chindynamics/Delta-Assistance/src/HCI/favoriteicons_rc.py

# Resource object code (Python 3)
# Created by: object code
# Created by: The Resource Compiler for Qt version 5.15.2
# WARNING! All changes made in this file will be lost!

from PySide6 import QtCore

qt_resource_data = b"\
\x00\x00\x01\xae\
<\
svg xmlns=\x22http:\
//www.w3.org/200\
0/svg\x22 width=\x2232\
\x22 height=\x2232\x22 vi\
ewBox=\x220 0 24 24\
\x22><path fill=\x22#f\
fffff\x22 d=\x22M11.07\
 12.85c.77-1.39 \
2.25-2.21 3.11-3\
.44c.91-1.29.4-3\
.7-2.18-3.7c-1.6\
9 0-2.52 1.28-2.\
87 2.34L6.54 6.9\
6C7.25 4.83 9.18\
 3 11.99 3c2.35 \
0 3.96 1.07 4.78\
 2.41c.7 1.15 1.\
11 3.3.03 4.9c-1\
.2 1.77-2.35 2.3\
1-2.97 3.45c-.25\
.46-.35.76-.35 2\
.24h-2.89c-.01-.\
78-.13-2.05.48-3\
.15M14 20c0 1.1-\
.9 2-2 2s-2-.9-2\
-2s.9-2 2-2s2 .9\
 2 2\x22/></svg>\
\x00\x00\x00\xf1\
<\
svg xmlns=\x22http:\
//www.w3.org/200\
0/svg\x22 width=\x2232\
\x22 height=\x2232\x22 vi\
ewBox=\x220 0 24 24\
\x22><path fill=\x22no\
ne\x22 stroke=\x22#fff\
fff\x22 stroke-line\
cap=\x22round\x22 stro\
ke-linejoin=\x22rou\
nd\x22 stroke-width\
=\x221.5\x22 d=\x22m17 17\
l4 4M3 11a8 8 0 \
1 0 16 0a8 8 0 0\
 0-16 0\x22/></svg>\
\
\x00\x00\x01t\
<\
svg xmlns=\x22http:\
//www.w3.org/200\
0/svg\x22 width=\x2232\
\x22 height=\x2232\x22 vi\
ewBox=\x220 0 24 24\
\x22><!-- Icon from\
 Huge Icons by H\
ugeicons - undef\
ined --><g fill=\
\x22none\x22 stroke=\x22#\
ffffff\x22 stroke-l\
inecap=\x22round\x22 s\
troke-linejoin=\x22\
round\x22 stroke-wi\
dth=\x221.5\x22 color=\
\x22#ffffff\x22><circl\
e cx=\x2212\x22 cy=\x2212\
\x22 r=\x2210\x22/><path \
d=\x22M8 12h8m-8 0c\
0-.7 1.994-2.008\
 2.5-2.5M8 12c0 \
.7 1.994 2.008 2\
.5 2.5\x22/></g></s\
vg>\
\x00\x00\x02,\
<\
svg xmlns=\x22http:\
//www.w3.org/200\
0/svg\x22 width=\x2232\
\x22 height=\x2232\x22 vi\
ewBox=\x220 0 24 24\
\x22><!-- Icon from\
 Google Material\
 Icons by Materi\
al Design Author\
s - https://gith\
ub.com/material-\
icons/material-i\
cons/blob/master\
/LICENSE --><pat\
h fill=\x22#ffffff\x22\
 d=\x22M22 12c0 5.5\
2-4.48 10-10 10S\
2 17.52 2 12c0-1\
.19.22-2.32.6-3.\
38l1.88.68C4.17 \
10.14 4 11.05 4 \
12c0 4.41 3.59 8\
 8 8s8-3.59 8-8s\
-3.59-8-8-8c-.95\
 0-1.85.17-2.69.\
48l-.68-1.89C9.6\
9 2.22 10.82 2 1\
2 2c5.52 0 10 4.\
48 10 10M5.5 4C4\
.67 4 4 4.67 4 5\
.5S4.67 7 5.5 7S\
7 6.33 7 5.5S6.3\
3 4 5.5 4M11 16V\
8H9v8zm4 0V8h-2v\
8z\x22/></svg>\
\x00\x00\x025\
<\
svg xmlns=\x22http:\
//www.w3.org/200\
0/svg\x22 width=\x2232\
\x22 height=\x2232\x22 vi\
ewBox=\x220 0 48 48\
\x22><!-- Icon from\
 Health Icons by\
 Resolve to Save\
 Lives - https:/\
/github.com/reso\
lvetosavelives/h\
ealthicons/blob/\
main/LICENSE -->\
<path fill=\x22#fff\
fff\x22 d=\x22M9 19.03\
5C9 13.309 12.81\
2 8 18.031 8c3.6\
22 0 6.31 2.382 \
7.969 5.761C27.6\
59 10.382 30.347\
 8 33.969 8C39.1\
89 8 43 13.31 43\
 19.035C43 31.28\
9 26 40 26 40s-1\
1.451-5.513-15.5\
57-14.556h10.142\
l1.612-2.865l1.8\
83 6.59l4.41-5.6\
69H34v-2h-6.49l-\
2.59 3.33l-2.117\
-7.409l-3.388 6.\
023H9.68q.32 1.0\
28.763 2H6v-2h3.\
68a14.8 14.8 0 0\
 1-.68-4.41\x22/></\
svg>\
\x00\x00\x02\xe0\
<\
svg xmlns=\x22http:\
//www.w3.org/200\
0/svg\x22 width=\x2232\
\x22 height=\x2232\x22 vi\
ewBox=\x220 0 24 24\
\x22><!-- Icon from\
 Huge Icons by H\
ugeicons - undef\
ined --><path fi\
ll=\x22none\x22 stroke\
=\x22#ffffff\x22 strok\
e-linecap=\x22round\
\x22 stroke-linejoi\
n=\x22round\x22 stroke\
-width=\x221.5\x22 d=\x22\
M2.008 15.81c.22\
3-3.494.88-6.05 \
1.435-7.535c.281\
-.75.885-1.308 1\
.658-1.495c4.3-1\
.04 9.498-1.04 1\
3.798 0c.773.187\
 1.377.745 1.658\
 1.495c.556 1.48\
5 1.212 4.041 1.\
435 7.534c.133 2\
.09-1.377 3.241-\
3.05 4.083c-1.06\
4.537-1.883-1.04\
6-2.427-2.272a1.\
82 1.82 0 0 0-1.\
687-1.084H9.172c\
-.739 0-1.39.415\
-1.687 1.084c-.5\
44 1.226-1.363 2\
.809-2.428 2.272\
c-1.655-.833-3.1\
83-1.976-3.049-4\
.083M5 4.5L6.963\
 4M19 4.5L17 4m-\
8 9l-1.5-1.5m0 0\
L6 10m1.5 1.5L6 \
13m1.5-1.5L9 10m\
6.988 0h.01m1.99\
 3h.01\x22 color=\x22#\
ffffff\x22/></svg>\
\x00\x00\x1b\x90\
<\
?xml version=\x221.\
0\x22 encoding=\x22utf\
-8\x22?>\x0a<!-- Gener\
ator: Adobe Adob\
e Illustrator 24\
.2.0, SVG Export\
 Plug-In . SVG V\
ersion: 6.00 Bui\
ld 0)  -->\x0a<svg \
version=\x221.1\x22 xm\
lns=\x22http://www.\
w3.org/2000/svg\x22\
 xmlns:xlink=\x22ht\
tp://www.w3.org/\
1999/xlink\x22 x=\x220\
px\x22 y=\x220px\x22\x0a\x09 wi\
dth=\x22595.28px\x22 h\
eight=\x22560.42px\x22\
 viewBox=\x220 0 59\
5.28 560.42\x22 sty\
le=\x22enable-backg\
round:new 0 0 59\
5.28 560.42;\x22\x0a\x09 \
xml:space=\x22prese\
rve\x22>\x0a<style typ\
e=\x22text/css\x22>\x0a\x09.\
st0{fill:#F4BAA6\
;stroke:#F4BAA6;\
stroke-width:5;s\
troke-miterlimit\
:10;}\x0a\x09.st1{disp\
lay:none;}\x0a\x09.st2\
{fill:#F4BAA6;st\
roke:#DB9E8A;str\
oke-width:5;stro\
ke-miterlimit:10\
;}\x0a\x09.st3{display\
:none;fill:#29AB\
E2;stroke:#00000\
0;stroke-width:5\
;stroke-miterlim\
it:10;}\x0a\x09.st4{fi\
ll:#E6E6E6;strok\
e:#E6E6E6;stroke\
-width:5;stroke-\
miterlimit:10;}\x0a\
\x09.st5{fill:#92CE\
E8;stroke:#92CEE\
8;stroke-width:5\
;stroke-miterlim\
it:10;}\x0a\x09.st6{fi\
ll:#29ABE2;strok\
e:#29ABE2;stroke\
-width:5;stroke-\
miterlimit:10;}\x0a\
\x09.st7{fill:#B3B3\
B3;stroke:#B3B3B\
3;stroke-width:5\
;stroke-miterlim\
it:10;}\x0a\x09.st8{fi\
ll:#E6E6E6;strok\
e:#D9D9D9;stroke\
-width:5;stroke-\
miterlimit:10;}\x0a\
\x09.st9{fill:#E6E6\
E6;stroke:#B3B3B\
3;stroke-width:5\
;stroke-miterlim\
it:10;}\x0a\x09.st10{f\
ill:#C48F7E;}\x0a\x09.\
st11{fill:#E6B5A\
5;}\x0a\x09.st12{fill:\
#F4BAA6;}\x0a\x09.st13\
{fill:#EDC1B2;}\x0a\
\x09.st14{fill:#F4B\
AA6;stroke:#F4BA\
A6;stroke-miterl\
imit:10;}\x0a\x09.st15\
{fill:#FF6B89;st\
roke:#FF6B89;str\
oke-miterlimit:1\
0;}\x0a\x09.st16{fill:\
none;stroke:#8A8\
A8A;stroke-width\
:5;stroke-miterl\
imit:10;}\x0a\x09.st17\
{fill:#92CEE8;}\x0a\
\x09.st18{fill:#F5F\
5F5;}\x0a\x09.st19{fil\
l:none;stroke:#9\
2CEE8;stroke-wid\
th:5;stroke-mite\
rlimit:10;}\x0a\x09.st\
20{fill:#855B4E;\
}\x0a\x09.st21{fill:#A\
37364;}\x0a\x09.st22{f\
ill:#EBCE42;}\x0a\x09.\
st23{fill:#94949\
4;stroke:#949494\
;stroke-width:5;\
stroke-miterlimi\
t:10;}\x0a\x09.st24{st\
roke:#000000;str\
oke-miterlimit:1\
0;}\x0a\x09.st25{fill:\
#F5F5F5;stroke:#\
F5F5F5;stroke-wi\
dth:5;stroke-mit\
erlimit:10;}\x0a\x09.s\
t26{fill:#FFFFFF\
;}\x0a\x09.st27{fill:#\
A37364;stroke:#A\
37364;stroke-wid\
th:5;stroke-mite\
rlimit:10;}\x0a\x09.st\
28{fill:#A37364;\
stroke:#A37364;s\
troke-width:3;st\
roke-miterlimit:\
10;}\x0a\x09.st29{fill\
:#6B9DB3;stroke:\
#6B9DB3;stroke-w\
idth:5;stroke-mi\
terlimit:10;}\x0a\x09.\
st30{fill:#DB9E8\
A;stroke:#346C85\
;stroke-width:5;\
stroke-miterlimi\
t:10;}\x0a\x09.st31{fi\
ll:#346C85;strok\
e:#346C85;stroke\
-width:5;stroke-\
miterlimit:10;}\x0a\
\x09.st32{fill:#2A6\
27A;stroke:#2A62\
7A;stroke-width:\
5;stroke-miterli\
mit:10;}\x0a\x09.st33{\
fill:#6B9DB3;}\x0a\x09\
.st34{fill:#EDED\
ED;}\x0a\x09.st35{fill\
:none;stroke:#32\
3E9C;stroke-widt\
h:7;stroke-miter\
limit:10;}\x0a\x09.st3\
6{fill:#C23A4E;}\
\x0a\x09.st37{fill:#C2\
3A4E;stroke:#C23\
A4E;stroke-miter\
limit:10;}\x0a\x09.st3\
8{fill:#C23A4E;s\
troke:#C23A4E;st\
roke-width:5;str\
oke-miterlimit:1\
0;}\x0a\x09.st39{fill:\
#8A8A8A;stroke:#\
323E9C;stroke-wi\
dth:7;stroke-mit\
erlimit:10;}\x0a\x09.s\
t40{fill:#323E9C\
;stroke:#323E9C;\
stroke-miterlimi\
t:10;}\x0a\x09.st41{fi\
ll:#79C77F;}\x0a\x09.s\
t42{opacity:0.72\
94;fill:#8DB9CC;\
}\x0a\x09.st43{fill:#D\
B9E8A;stroke:#DB\
9E8A;stroke-mite\
rlimit:10;}\x0a\x09.st\
44{opacity:0.588\
2;fill:#FFFF00;}\
\x0a\x09.st45{fill:#8C\
C63F;stroke:#8CC\
63F;stroke-miter\
limit:10;}\x0a\x09.st4\
6{fill:#FF0000;}\
\x0a\x09.st47{fill:#C1\
272D;}\x0a\x09.st48{fi\
ll:#8CC63F;strok\
e:#80B53A;stroke\
-miterlimit:10;}\
\x0a\x09.st49{opacity:\
0.9608;fill:#FF0\
000;}\x0a\x09.st50{opa\
city:0.949;fill:\
#C1272D;}\x0a\x09.st51\
{fill:#FFFD7A;st\
roke:#FFFD7A;str\
oke-miterlimit:1\
0;}\x0a\x09.st52{fill:\
#8CC63F;}\x0a\x09.st53\
{fill:#B38576;st\
roke:#B38576;str\
oke-miterlimit:1\
0;}\x0a\x09.st54{opaci\
ty:0.7412;fill:#\
9E68A3;stroke:#9\
E68A3;stroke-mit\
erlimit:10;}\x0a\x09.s\
t55{opacity:0.50\
2;stroke:#000000\
;stroke-miterlim\
it:10;}\x0a\x09.st56{f\
ill:#C48F7E;stro\
ke:#C48F7E;strok\
e-miterlimit:10;\
}\x0a\x09.st57{fill:#8\
55B4E;stroke:#85\
5B4E;stroke-mite\
rlimit:10;}\x0a\x09.st\
58{opacity:0.670\
6;fill:#F15A24;}\
\x0a\x09.st59{fill:#9E\
005D;}\x0a\x09.st60{op\
acity:0.6784;fil\
l:#FFFFFF;stroke\
:#FFFFFF;stroke-\
miterlimit:10;}\x0a\
\x09.st61{opacity:0\
.6588;fill:#FFFD\
7A;stroke:#FFFD7\
A;stroke-miterli\
mit:10;}\x0a\x09.st62{\
fill:#949494;str\
oke:#949494;stro\
ke-miterlimit:10\
;}\x0a\x09.st63{fill:n\
one;stroke:#9494\
94;stroke-width:\
3;stroke-miterli\
mit:10;}\x0a\x09.st64{\
fill:#FFFD7A;str\
oke:#EDEB77;stro\
ke-miterlimit:10\
;}\x0a\x09.st65{fill:#\
FF9191;stroke:#F\
F9191;stroke-mit\
erlimit:10;}\x0a\x09.s\
t66{fill:#FFFFFF\
;stroke:#FFFFFF;\
stroke-miterlimi\
t:10;}\x0a</style>\x0a\
<g id=\x22Layer_1\x22>\
\x0a</g>\x0a<g id=\x22Lay\
er_2\x22>\x0a</g>\x0a<g i\
d=\x22Layer_3\x22>\x0a\x09<p\
ath class=\x22st11\x22\
 d=\x22M180.65,344.\
7l0.71-35.33c0.0\
5-2.59,1.79-4.83\
,4.29-5.53l9.46-\
2.64c18.97-5.29,\
36.82,11.33,32.9\
1,30.63l0,0\x0a\x09\x09l3\
6.18,44.04c2.99,\
3.64,0.56,9.13-4\
.15,9.37l-37.96,\
1.88c-8.69,0.43-\
17.12-3.05-22.97\
-9.49l-10.42-11.\
47\x0a\x09\x09C183.37,360\
.3,180.49,352.62\
,180.65,344.7z\x22/\
>\x0a\x09<path class=\x22\
st12\x22 d=\x22M247.04\
,394.39l-0.54-3.\
41l-40.21-45.27c\
-7.24-8.15-7.34-\
20.89-0.22-29.17\
l0,0\x0a\x09\x09c13.74-15\
.99,36.93-17.32,\
52.2-2.99l32.7,3\
0.7c4.34,4.08,9.\
77,6.61,15.53,7.\
23l27.08,2.93c6.\
66,0.72,12.96,3.\
55,18.1,8.12\x0a\x09\x09l\
6.94,6.16c6.2,5.\
5,3.93,16.19-3.8\
8,18.31l-85.03,2\
3.12C259.3,412.9\
6,248.84,405.7,2\
47.04,394.39z\x22/>\
\x0a\x09<path class=\x22s\
t13\x22 d=\x22M215.82,\
380.45l-34.68-35\
.97c-1.58-1.64-2\
.63-3.71-3.03-5.\
94l-0.22-1.23c-4\
.15-23.47-27.48-\
38.39-50.53-32.3\
1\x0a\x09\x09l-5.63,1.48l\
9.1,44.63l34.3,3\
2.64L215.82,380.\
45z\x22/>\x0a\x09<path cl\
ass=\x22st14\x22 d=\x22M5\
15.8,452.48l-335\
.96-1.12c-9.87-0\
.03-19.33-3.97-2\
6.31-10.95l-65.5\
3-65.49\x0a\x09\x09c-5.45\
-5.44-8.51-12.83\
-8.51-20.53v-36.\
17c0-10.6,8.5-19\
.23,19.1-19.39h0\
c18.13-0.28,33.8\
1,12.57,37.1,30.\
4l2.06,11.2\x0a\x09\x09c0\
.37,2.02,1.35,3.\
88,2.8,5.33l30.8\
4,30.82c2.52,2.5\
2,5.96,3.91,9.52\
,3.85l63.29-2.06\
l271.59-16.02V45\
2.48z\x22/>\x0a\x09<path \
class=\x22st15\x22 d=\x22\
M275.05,55.15l-1\
0.86-2.92c-23.91\
-9.32-71.75,11.0\
8-86.84,31.76l-1\
3.36,19.61\x0a\x09\x09c-2\
0.8,28.51-10.53,\
69.43,12.09,96.5\
3L296.16,323.8c9\
.4,11.26,26.88,1\
0.86,35.75-0.81l\
123.64-136.55\x0a\x09\x09\
c23.73-31.23,6.4\
1-88.83-19.84-11\
8l0,0c-14.85-16.\
5-53.52-29.92-74\
.12-21.55l-13.68\
,6.98c-2.88,0.9-\
5.64,2.14-8.23,3\
.7\x0a\x09\x09l-27.23,16.\
42c-2.17,0.88-9.\
43-4.3-16.47-9.1\
6C289.61,60.43,2\
82.53,57.16,275.\
05,55.15z\x22/>\x0a\x09<p\
ath class=\x22st16\x22\
 d=\x22M178.85,203.\
03l43.23-0.58l1.\
26-0.45l15.62-57\
.5c0.06-0.21,0.3\
5-0.21,0.41-0.01\
l34.29,110.6\x0a\x09\x09c\
0.12,0.4,0.7,0.3\
5,0.76-0.06l21.6\
9-142.46c0.05-0.\
3,0.47-0.32,0.54\
-0.02l21.13,85.6\
3c0.28,1.15,1.26\
,2,2.44,2.12l22.\
31-0.01\x22/>\x0a\x09<pol\
ygon class=\x22st17\
\x22 points=\x22342.17\
,185.73 359.19,1\
82.05 376.3,179 \
387.04,177.12 40\
1.83,175.96 415.\
03,176.97 426.78\
,178.13 \x0a\x09\x09438.8\
2,179.58 448.1,1\
81.9 459.85,184.\
08 470.3,187.27 \
474.94,191.77 47\
3.2,214.83 473.0\
5,232.24 468.99,\
253.85 463.19,26\
9.66 \x0a\x09\x09455.94,2\
82.28 448.83,291\
.56 440.41,299.9\
7 432.87,307.52 \
423.01,314.91 41\
2.57,322.6 402.8\
5,324.2 395.16,3\
18.54 387.62,308\
.97 \x0a\x09\x09380.07,30\
6.79 367.75,295.\
04 358.61,284.6 \
350.19,275.32 34\
6.13,260.96 342.\
36,247.76 341.06\
,232.53 340.62,2\
14.25 340.77,199\
.46 \x09\x0a\x09\x09\x22/>\x0a\x09<pa\
th class=\x22st18\x22 \
d=\x22M393.78,178.4\
1h27.94c0.29,0,0\
.52,0.24,0.52,0.\
52v140.95c0,0.29\
-0.24,0.52-0.52,\
0.52l-15.75,7.28\
l-12.2-7.28\x0a\x09\x09c-\
0.29,0-0.52-0.24\
-0.52-0.52V178.9\
4C393.26,178.65,\
393.49,178.41,39\
3.78,178.41z\x22/>\x0a\
\x09<rect x=\x22343.96\
\x22 y=\x22221.07\x22 cla\
ss=\x22st18\x22 width=\
\x22129.5\x22 height=\x22\
28.99\x22/>\x0a\x09<path \
class=\x22st19\x22 d=\x22\
M340.75,189.22l2\
.24,55.4c0.81,20\
.12,10.04,38.91,\
25.34,51.65l29.6\
9,24.7c5.25,4.36\
,12.76,4.46,18.1\
,0.22\x0a\x09\x09l20.02-1\
5.87c23.11-18.32\
,36.93-46.25,37.\
63-76.08l0.88-37\
.23c0.89-1.78-0.\
01-3.95-1.88-4.5\
6l-5.66-1.84\x0a\x09\x09c\
-37.14-12.06-76.\
89-13.01-114.54-\
2.73l-10.24,2.8C\
340.84,186.09,34\
0.07,187.79,340.\
75,189.22z\x22/>\x0a\x09<\
line class=\x22st16\
\x22 x1=\x22359.68\x22 y1\
=\x22155.02\x22 x2=\x2235\
9.4\x22 y2=\x22116.26\x22\
/>\x0a\x09<line class=\
\x22st16\x22 x1=\x22342.1\
7\x22 y1=\x22135.64\x22 x\
2=\x22376.33\x22 y2=\x221\
35.64\x22/>\x0a</g>\x0a<g\
 id=\x22Layer_5\x22>\x0a\x09\
<g id=\x22Layer_4\x22>\
\x0a\x09</g>\x0a</g>\x0a<g i\
d=\x22Layer_6\x22>\x0a</g\
>\x0a<g id=\x22Layer_7\
\x22>\x0a</g>\x0a</svg>\x0a\
\x00\x00)\x09\
<\
?xml version=\x221.\
0\x22 encoding=\x22utf\
-8\x22?>\x0a<!-- Gener\
ator: Adobe Adob\
e Illustrator 24\
.2.0, SVG Export\
 Plug-In . SVG V\
ersion: 6.00 Bui\
ld 0)  -->\x0a<svg \
version=\x221.1\x22 xm\
lns=\x22http://www.\
w3.org/2000/svg\x22\
 xmlns:xlink=\x22ht\
tp://www.w3.org/\
1999/xlink\x22 x=\x220\
px\x22 y=\x220px\x22\x0a\x09 wi\
dth=\x22595.28px\x22 h\
eight=\x22555.8px\x22 \
viewBox=\x220 0 595\
.28 555.8\x22 style\
=\x22enable-backgro\
und:new 0 0 595.\
28 555.8;\x22\x0a\x09 xml\
:space=\x22preserve\
\x22>\x0a<style type=\x22\
text/css\x22>\x0a\x09.st0\
{fill:#F4BAA6;st\
roke:#F4BAA6;str\
oke-width:5;stro\
ke-miterlimit:10\
;}\x0a\x09.st1{display\
:none;}\x0a\x09.st2{fi\
ll:#F4BAA6;strok\
e:#DB9E8A;stroke\
-width:5;stroke-\
miterlimit:10;}\x0a\
\x09.st3{display:no\
ne;fill:#29ABE2;\
stroke:#000000;s\
troke-width:5;st\
roke-miterlimit:\
10;}\x0a\x09.st4{fill:\
#E6E6E6;stroke:#\
E6E6E6;stroke-wi\
dth:5;stroke-mit\
erlimit:10;}\x0a\x09.s\
t5{fill:#92CEE8;\
stroke:#92CEE8;s\
troke-width:5;st\
roke-miterlimit:\
10;}\x0a\x09.st6{fill:\
#29ABE2;stroke:#\
29ABE2;stroke-wi\
dth:5;stroke-mit\
erlimit:10;}\x0a\x09.s\
t7{fill:#B3B3B3;\
stroke:#B3B3B3;s\
troke-width:5;st\
roke-miterlimit:\
10;}\x0a\x09.st8{fill:\
#E6E6E6;stroke:#\
D9D9D9;stroke-wi\
dth:5;stroke-mit\
erlimit:10;}\x0a\x09.s\
t9{fill:#E6E6E6;\
stroke:#B3B3B3;s\
troke-width:5;st\
roke-miterlimit:\
10;}\x0a\x09.st10{fill\
:#C48F7E;}\x0a\x09.st1\
1{fill:#E6B5A5;}\
\x0a\x09.st12{fill:#F4\
BAA6;}\x0a\x09.st13{fi\
ll:#EDC1B2;}\x0a\x09.s\
t14{fill:#F4BAA6\
;stroke:#F4BAA6;\
stroke-miterlimi\
t:10;}\x0a\x09.st15{fi\
ll:#FF6B89;strok\
e:#FF6B89;stroke\
-miterlimit:10;}\
\x0a\x09.st16{fill:non\
e;stroke:#8A8A8A\
;stroke-width:5;\
stroke-miterlimi\
t:10;}\x0a\x09.st17{fi\
ll:#92CEE8;}\x0a\x09.s\
t18{fill:#F5F5F5\
;}\x0a\x09.st19{fill:n\
one;stroke:#92CE\
E8;stroke-width:\
5;stroke-miterli\
mit:10;}\x0a\x09.st20{\
fill:#855B4E;}\x0a\x09\
.st21{fill:#A373\
64;}\x0a\x09.st22{fill\
:#EBCE42;}\x0a\x09.st2\
3{fill:#949494;s\
troke:#949494;st\
roke-width:5;str\
oke-miterlimit:1\
0;}\x0a\x09.st24{strok\
e:#000000;stroke\
-miterlimit:10;}\
\x0a\x09.st25{fill:#F5\
F5F5;stroke:#F5F\
5F5;stroke-width\
:5;stroke-miterl\
imit:10;}\x0a\x09.st26\
{fill:#FFFFFF;}\x0a\
\x09.st27{fill:#A37\
364;stroke:#A373\
64;stroke-width:\
5;stroke-miterli\
mit:10;}\x0a\x09.st28{\
fill:#A37364;str\
oke:#A37364;stro\
ke-width:3;strok\
e-miterlimit:10;\
}\x0a\x09.st29{fill:#6\
B9DB3;stroke:#6B\
9DB3;stroke-widt\
h:5;stroke-miter\
limit:10;}\x0a\x09.st3\
0{fill:#DB9E8A;s\
troke:#346C85;st\
roke-width:5;str\
oke-miterlimit:1\
0;}\x0a\x09.st31{fill:\
#346C85;stroke:#\
346C85;stroke-wi\
dth:5;stroke-mit\
erlimit:10;}\x0a\x09.s\
t32{fill:#2A627A\
;stroke:#2A627A;\
stroke-width:5;s\
troke-miterlimit\
:10;}\x0a\x09.st33{fil\
l:#6B9DB3;}\x0a\x09.st\
34{fill:#EDEDED;\
}\x0a\x09.st35{fill:no\
ne;stroke:#323E9\
C;stroke-width:7\
;stroke-miterlim\
it:10;}\x0a\x09.st36{f\
ill:#C23A4E;}\x0a\x09.\
st37{fill:#C23A4\
E;stroke:#C23A4E\
;stroke-miterlim\
it:10;}\x0a\x09.st38{f\
ill:#C23A4E;stro\
ke:#C23A4E;strok\
e-width:5;stroke\
-miterlimit:10;}\
\x0a\x09.st39{fill:#8A\
8A8A;stroke:#323\
E9C;stroke-width\
:7;stroke-miterl\
imit:10;}\x0a\x09.st40\
{fill:#323E9C;st\
roke:#323E9C;str\
oke-miterlimit:1\
0;}\x0a\x09.st41{fill:\
#79C77F;}\x0a\x09.st42\
{opacity:0.7294;\
fill:#8DB9CC;}\x0a\x09\
.st43{fill:#DB9E\
8A;stroke:#DB9E8\
A;stroke-miterli\
mit:10;}\x0a\x09.st44{\
opacity:0.5882;f\
ill:#FFFF00;}\x0a\x09.\
st45{fill:#8CC63\
F;stroke:#8CC63F\
;stroke-miterlim\
it:10;}\x0a\x09.st46{f\
ill:#FF0000;}\x0a\x09.\
st47{fill:#C1272\
D;}\x0a\x09.st48{fill:\
#8CC63F;stroke:#\
80B53A;stroke-mi\
terlimit:10;}\x0a\x09.\
st49{opacity:0.9\
608;fill:#FF0000\
;}\x0a\x09.st50{opacit\
y:0.949;fill:#C1\
272D;}\x0a\x09.st51{fi\
ll:#FFFD7A;strok\
e:#FFFD7A;stroke\
-miterlimit:10;}\
\x0a\x09.st52{fill:#8C\
C63F;}\x0a\x09.st53{fi\
ll:#B38576;strok\
e:#B38576;stroke\
-miterlimit:10;}\
\x0a\x09.st54{opacity:\
0.7412;fill:#9E6\
8A3;stroke:#9E68\
A3;stroke-miterl\
imit:10;}\x0a\x09.st55\
{opacity:0.502;s\
troke:#000000;st\
roke-miterlimit:\
10;}\x0a\x09.st56{fill\
:#C48F7E;stroke:\
#C48F7E;stroke-m\
iterlimit:10;}\x0a\x09\
.st57{fill:#855B\
4E;stroke:#855B4\
E;stroke-miterli\
mit:10;}\x0a\x09.st58{\
opacity:0.6706;f\
ill:#F15A24;}\x0a\x09.\
st59{fill:#9E005\
D;}\x0a\x09.st60{opaci\
ty:0.6784;fill:#\
FFFFFF;stroke:#F\
FFFFF;stroke-mit\
erlimit:10;}\x0a\x09.s\
t61{opacity:0.65\
88;fill:#FFFD7A;\
stroke:#FFFD7A;s\
troke-miterlimit\
:10;}\x0a\x09.st62{fil\
l:#949494;stroke\
:#949494;stroke-\
miterlimit:10;}\x0a\
\x09.st63{fill:none\
;stroke:#949494;\
stroke-width:3;s\
troke-miterlimit\
:10;}\x0a\x09.st64{fil\
l:#FFFD7A;stroke\
:#EDEB77;stroke-\
miterlimit:10;}\x0a\
\x09.st65{fill:#FF9\
191;stroke:#FF91\
91;stroke-miterl\
imit:10;}\x0a\x09.st66\
{fill:#FFFFFF;st\
roke:#FFFFFF;str\
oke-miterlimit:1\
0;}\x0a</style>\x0a<g \
id=\x22Layer_1\x22>\x0a</\
g>\x0a<g id=\x22Layer_\
2\x22>\x0a</g>\x0a<g id=\x22\
Layer_3\x22>\x0a</g>\x0a<\
g id=\x22Layer_5\x22>\x0a\
\x09<g id=\x22Layer_4\x22\
>\x0a\x09</g>\x0a</g>\x0a<g \
id=\x22Layer_6\x22>\x0a\x09<\
ellipse class=\x22s\
t33\x22 cx=\x22297.64\x22\
 cy=\x22233.69\x22 rx=\
\x22167\x22 ry=\x22167.5\x22\
/>\x0a\x09<path class=\
\x22st42\x22 d=\x22M301.5\
7,205.2l-2.35-92\
.93c-0.4-15.83,1\
3.13-28.27,28.45\
-26.17l0,0c52.19\
,7.14,103.21,53.\
94,115.47,106.37\
\x0a\x09\x09l2.02,10.71c0\
,14.17-12.86,23.\
64-25.47,23.65l-\
96.32,0.1C311.55\
,226.94,301.88,2\
17.3,301.57,205.\
2z\x22/>\x0a\x09<path cla\
ss=\x22st42\x22 d=\x22M29\
0.78,205.2l2.4-9\
2.93C293.6,96.44\
,279.75,84,264.0\
6,86.1l0,0c-53.4\
4,7.14-96.96,46.\
44-109.51,98.87\x0a\
\x09\x09l-4.12,17.21c-\
3.01,12.56,6.51,\
24.64,19.43,24.6\
5l98.61,0.1C280.\
56,226.94,290.47\
,217.3,290.78,20\
5.2z\x22/>\x0a\x09<path c\
lass=\x22st42\x22 d=\x22M\
157.44,286.84c-9\
.12-22.42-4.92-3\
4.8,0.61-40.99c6\
.75-7.55,17.76-8\
.12,35.37-7.05\x0a\x09\
\x09c10.93,0.67,12.\
15,0.83,39.19-0.\
11c29.62-1.03,51\
.92,0.21,87.57,0\
.21c51.26,0,90.7\
8-2.08,115.1,3.8\
2\x0a\x09\x09c12.73,3.09,\
13.47,17.16,7.15\
,35.63c-7.79,22.\
79-29.52,57.25-4\
7.25,69.8c-18.26\
,12.92-25.24,18.\
09-38.12,23.29\x0a\x09\
\x09c-9.82,3.96-22.\
84,8.98-48.12,11\
.3c-34.99,3.2-62\
.87-7.78-86.15-2\
1.51C191.74,342.\
89,169.68,316.93\
,157.44,286.84z\x22\
/>\x0a\x09<path class=\
\x22st44\x22 d=\x22M359.3\
2,272.77l12.21-1\
7.04c2.64-3.69,6\
.89-5.72,11.29-5\
.4l17.97,1.31c5.\
85,0.43,11.06,4.\
03,13.72,9.49\x0a\x09\x09\
l7.53,15.46c2.43\
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
,23.07-21.94,37.\
56-24.98c14.49-3\
.04,29.14-0.55,4\
2.52,8.19\x0a\x09\x09l15.\
84,10.35c9.49,6.\
2,28.56,11.71,32\
.95,21.31c7.99,1\
7.46-4.78,41.51-\
16.05,58.77l-1.5\
7,0c-8.74,13.38-\
19.01,14.94-33.1\
3,17.98\x0a\x09\x09s-23.9\
1-0.77-38.32-10.\
19l-20.77-7.35c-\
15.96-10.43-30.6\
3-23.26-32.31-39\
.21C171.97,291.6\
6,179.35,278.37,\
186.4,267.58z\x22/>\
\x0a\x09<path class=\x22s\
t59\x22 d=\x22M328.27,\
279.61l13.94,8.9\
3c6.55,2.39,11.5\
8,5.89,16.94,10.\
36l8.21,5.86c12.\
59,10.49,11.38,3\
0.19-2.4,39.05\x0a\x09\
\x09l-40.22,24.51c-\
14.52,9.34-33.34\
-2.57-31.11-19.6\
9l4.02-50.41C299\
.54,283.64,314.4\
6,274.58,328.27,\
279.61z\x22/>\x0a\x09<pat\
h class=\x22st60\x22 d\
=\x22M198.41,310.78\
c-4.02-21.71-7.6\
4-52.03,15.62-52\
.03c10.18,0,25.7\
7,3.76,37.85,12.\
2\x0a\x09\x09c15.52,10.84\
,26.53,28.09,26.\
53,41.18c0,23.27\
-4.61,38.12-27.8\
8,38.12c-8.4,0-2\
4.31-5.66-30.87-\
9.5\x0a\x09\x09C208.05,33\
3.96,201.12,325.\
4,198.41,310.78z\
\x22/>\x0a\x09\x0a\x09\x09<ellipse\
 transform=\x22matr\
ix(0.8164 -0.577\
4 0.5774 0.8164 \
-136.8947 197.37\
63)\x22 class=\x22st61\
\x22 cx=\x22241.99\x22 cy\
=\x22314\x22 rx=\x2217.25\
\x22 ry=\x2223.25\x22/>\x0a\x09\
<line class=\x22st6\
2\x22 x1=\x22345.23\x22 y\
1=\x22331.13\x22 x2=\x223\
52.93\x22 y2=\x22323.4\
3\x22/>\x0a\x09<line clas\
s=\x22st62\x22 x1=\x22325\
.08\x22 y1=\x22334.14\x22\
 x2=\x22317.76\x22 y2=\
\x22341.46\x22/>\x0a\x09<lin\
e class=\x22st62\x22 x\
1=\x22321.42\x22 y1=\x223\
03.12\x22 x2=\x22313.7\
6\x22 y2=\x22310.78\x22/>\
\x0a\x09<line class=\x22s\
t62\x22 x1=\x22334.85\x22\
 y1=\x22314\x22 x2=\x2234\
1.9\x22 y2=\x22306.95\x22\
/>\x0a\x09<line class=\
\x22st62\x22 x1=\x22302.1\
4\x22 y1=\x22341.46\x22 x\
2=\x22309.46\x22 y2=\x223\
34.14\x22/>\x0a\x09<line \
class=\x22st62\x22 x1=\
\x22321.42\x22 y1=\x22360\
.21\x22 x2=\x22330.06\x22\
 y2=\x22351.58\x22/>\x0a\x09\
<line class=\x22st6\
2\x22 x1=\x22343.08\x22 y\
1=\x22346.67\x22 x2=\x223\
48.3\x22 y2=\x22341.46\
\x22/>\x0a\x09<path class\
=\x22st63\x22 d=\x22M374.\
18,279.92c15.89,\
0,10.27,14.87,9.\
26,16.93\x22/>\x0a\x09<pa\
th class=\x22st63\x22 \
d=\x22M398.39,276.2\
4c-10.85,11.6-17\
.87-2.66-18.69-4\
.81\x22/>\x0a\x09<path cl\
ass=\x22st63\x22 d=\x22M3\
90.05,296.47c-3.\
49-15.5,12.25-13\
.28,14.48-12.75\x22\
/>\x0a\x09<path class=\
\x22st64\x22 d=\x22M173.3\
9,196.76c0.56,0.\
79,1.64,1.01,2.4\
6,0.5l58.98-36.7\
2l4.39-2.81l-1.7\
7-4.87\x0a\x09\x09c-6.41-\
13.87-33.05-13.7\
2-46.36-6.21c-11\
.49,6.48-13.62,7\
.97-20.38,15.75c\
-1.6,1.84-5.68,1\
1.47-6.49,13.69\x0a\
\x09\x09c-1.25,3.41-0.\
53,6.78,1.56,9.8\
7L173.39,196.76z\
\x22/>\x0a\x09<path class\
=\x22st10\x22 d=\x22M198.\
27,216.08l37.95-\
23.65l-5.91-1.65\
c-15.55-1.78-29.\
8,8.84-32.54,24.\
24L198.27,216.08\
z\x22/>\x0a\x09<path clas\
s=\x22st10\x22 d=\x22M185\
.52,191.04l37.95\
-23.65l-5.91-1.6\
5c-15.55-1.78-29\
.8,8.84-32.54,24\
.24L185.52,191.0\
4z\x22/>\x0a</g>\x0a<g id\
=\x22Layer_7\x22>\x0a</g>\
\x0a</svg>\x0a\
\x00\x00\x01\x0a\
<\
svg xmlns=\x22http:\
//www.w3.org/200\
0/svg\x22 width=\x2232\
\x22 height=\x2232\x22 vi\
ewBox=\x220 0 24 24\
\x22><path fill=\x22#f\
fffff\x22 d=\x22M10.09\
 15.59L11.5 17l5\
-5l-5-5l-1.41 1.\
41L12.67 11H3v2h\
9.67zM19 3H5a2 2\
 0 0 0-2 2v4h2V5\
h14v14H5v-4H3v4a\
2 2 0 0 0 2 2h14\
c1.1 0 2-.9 2-2V\
5c0-1.1-.9-2-2-2\
\x22/></svg>\
\x00\x00\x15\x0e\
<\
?xml version=\x221.\
0\x22 encoding=\x22utf\
-8\x22?>\x0a<!-- Gener\
ator: Adobe Adob\
e Illustrator 24\
.2.0, SVG Export\
 Plug-In . SVG V\
ersion: 6.00 Bui\
ld 0)  -->\x0a<svg \
version=\x221.1\x22 xm\
lns=\x22http://www.\
w3.org/2000/svg\x22\
 xmlns:xlink=\x22ht\
tp://www.w3.org/\
1999/xlink\x22 x=\x220\
px\x22 y=\x220px\x22\x0a\x09 wi\
dth=\x22595.28px\x22 h\
eight=\x22550px\x22 vi\
ewBox=\x220 0 595.2\
8 550\x22 style=\x22en\
able-background:\
new 0 0 595.28 5\
50;\x22 xml:space=\x22\
preserve\x22>\x0a<styl\
e type=\x22text/css\
\x22>\x0a\x09.st0{fill:#F\
4BAA6;stroke:#F4\
BAA6;stroke-widt\
h:5;stroke-miter\
limit:10;}\x0a\x09.st1\
{display:none;}\x0a\
\x09.st2{fill:#F4BA\
A6;stroke:#DB9E8\
A;stroke-width:5\
;stroke-miterlim\
it:10;}\x0a\x09.st3{di\
splay:none;fill:\
#29ABE2;stroke:#\
000000;stroke-wi\
dth:5;stroke-mit\
erlimit:10;}\x0a\x09.s\
t4{fill:#E6E6E6;\
stroke:#E6E6E6;s\
troke-width:5;st\
roke-miterlimit:\
10;}\x0a\x09.st5{fill:\
#92CEE8;stroke:#\
92CEE8;stroke-wi\
dth:5;stroke-mit\
erlimit:10;}\x0a\x09.s\
t6{fill:#29ABE2;\
stroke:#29ABE2;s\
troke-width:5;st\
roke-miterlimit:\
10;}\x0a\x09.st7{fill:\
#B3B3B3;stroke:#\
B3B3B3;stroke-wi\
dth:5;stroke-mit\
erlimit:10;}\x0a\x09.s\
t8{fill:#E6E6E6;\
stroke:#D9D9D9;s\
troke-width:5;st\
roke-miterlimit:\
10;}\x0a\x09.st9{fill:\
#E6E6E6;stroke:#\
B3B3B3;stroke-wi\
dth:5;stroke-mit\
erlimit:10;}\x0a\x09.s\
t10{fill:#C48F7E\
;}\x0a\x09.st11{fill:#\
E6B5A5;}\x0a\x09.st12{\
fill:#F4BAA6;}\x0a\x09\
.st13{fill:#EDC1\
B2;}\x0a\x09.st14{fill\
:#F4BAA6;stroke:\
#F4BAA6;stroke-m\
iterlimit:10;}\x0a\x09\
.st15{fill:#FF6B\
89;stroke:#FF6B8\
9;stroke-miterli\
mit:10;}\x0a\x09.st16{\
fill:none;stroke\
:#8A8A8A;stroke-\
width:5;stroke-m\
iterlimit:10;}\x0a\x09\
.st17{fill:#92CE\
E8;}\x0a\x09.st18{fill\
:#F5F5F5;}\x0a\x09.st1\
9{fill:none;stro\
ke:#92CEE8;strok\
e-width:5;stroke\
-miterlimit:10;}\
\x0a\x09.st20{fill:#85\
5B4E;}\x0a\x09.st21{fi\
ll:#A37364;}\x0a\x09.s\
t22{fill:#EBCE42\
;}\x0a\x09.st23{fill:#\
949494;stroke:#9\
49494;stroke-wid\
th:5;stroke-mite\
rlimit:10;}\x0a\x09.st\
24{stroke:#00000\
0;stroke-miterli\
mit:10;}\x0a\x09.st25{\
fill:#F5F5F5;str\
oke:#F5F5F5;stro\
ke-width:5;strok\
e-miterlimit:10;\
}\x0a\x09.st26{fill:#F\
FFFFF;}\x0a\x09.st27{f\
ill:#A37364;stro\
ke:#A37364;strok\
e-width:5;stroke\
-miterlimit:10;}\
\x0a\x09.st28{fill:#A3\
7364;stroke:#A37\
364;stroke-width\
:3;stroke-miterl\
imit:10;}\x0a\x09.st29\
{fill:#6B9DB3;st\
roke:#6B9DB3;str\
oke-width:5;stro\
ke-miterlimit:10\
;}\x0a\x09.st30{fill:#\
DB9E8A;stroke:#3\
46C85;stroke-wid\
th:5;stroke-mite\
rlimit:10;}\x0a\x09.st\
31{fill:#346C85;\
stroke:#346C85;s\
troke-width:5;st\
roke-miterlimit:\
10;}\x0a\x09.st32{fill\
:#2A627A;stroke:\
#2A627A;stroke-w\
idth:5;stroke-mi\
terlimit:10;}\x0a\x09.\
st33{fill:#6B9DB\
3;}\x0a\x09.st34{fill:\
#EDEDED;}\x0a\x09.st35\
{fill:none;strok\
e:#323E9C;stroke\
-width:7;stroke-\
miterlimit:10;}\x0a\
\x09.st36{fill:#C23\
A4E;}\x0a\x09.st37{fil\
l:#C23A4E;stroke\
:#C23A4E;stroke-\
miterlimit:10;}\x0a\
\x09.st38{fill:#C23\
A4E;stroke:#C23A\
4E;stroke-width:\
5;stroke-miterli\
mit:10;}\x0a\x09.st39{\
fill:#8A8A8A;str\
oke:#323E9C;stro\
ke-width:7;strok\
e-miterlimit:10;\
}\x0a\x09.st40{fill:#3\
23E9C;stroke:#32\
3E9C;stroke-mite\
rlimit:10;}\x0a\x09.st\
41{fill:#79C77F;\
}\x0a\x09.st42{opacity\
:0.7294;fill:#8D\
B9CC;}\x0a\x09.st43{fi\
ll:#DB9E8A;strok\
e:#DB9E8A;stroke\
-miterlimit:10;}\
\x0a\x09.st44{opacity:\
0.5882;fill:#FFF\
F00;}\x0a\x09.st45{fil\
l:#8CC63F;stroke\
:#8CC63F;stroke-\
miterlimit:10;}\x0a\
\x09.st46{fill:#FF0\
000;}\x0a\x09.st47{fil\
l:#C1272D;}\x0a\x09.st\
48{fill:#8CC63F;\
stroke:#80B53A;s\
troke-miterlimit\
:10;}\x0a\x09.st49{opa\
city:0.9608;fill\
:#FF0000;}\x0a\x09.st5\
0{opacity:0.949;\
fill:#C1272D;}\x0a\x09\
.st51{fill:#FFFD\
7A;stroke:#FFFD7\
A;stroke-miterli\
mit:10;}\x0a\x09.st52{\
fill:#8CC63F;}\x0a\x09\
.st53{fill:#B385\
76;stroke:#B3857\
6;stroke-miterli\
mit:10;}\x0a\x09.st54{\
opacity:0.7412;f\
ill:#9E68A3;stro\
ke:#9E68A3;strok\
e-miterlimit:10;\
}\x0a\x09.st55{opacity\
:0.502;stroke:#0\
00000;stroke-mit\
erlimit:10;}\x0a\x09.s\
t56{fill:#C48F7E\
;stroke:#C48F7E;\
stroke-miterlimi\
t:10;}\x0a\x09.st57{fi\
ll:#855B4E;strok\
e:#855B4E;stroke\
-miterlimit:10;}\
\x0a\x09.st58{opacity:\
0.6706;fill:#F15\
A24;}\x0a\x09.st59{fil\
l:#9E005D;}\x0a\x09.st\
60{opacity:0.678\
4;fill:#FFFFFF;s\
troke:#FFFFFF;st\
roke-miterlimit:\
10;}\x0a\x09.st61{opac\
ity:0.6588;fill:\
#FFFD7A;stroke:#\
FFFD7A;stroke-mi\
terlimit:10;}\x0a\x09.\
st62{fill:#94949\
4;stroke:#949494\
;stroke-miterlim\
it:10;}\x0a\x09.st63{f\
ill:none;stroke:\
#949494;stroke-w\
idth:3;stroke-mi\
terlimit:10;}\x0a\x09.\
st64{fill:#FFFD7\
A;stroke:#EDEB77\
;stroke-miterlim\
it:10;}\x0a\x09.st65{f\
ill:#FF9191;stro\
ke:#FF9191;strok\
e-miterlimit:10;\
}\x0a\x09.st66{fill:#F\
FFFFF;stroke:#FF\
FFFF;stroke-mite\
rlimit:10;}\x0a</st\
yle>\x0a<g id=\x22Laye\
r_1\x22>\x0a</g>\x0a<g id\
=\x22Layer_2\x22>\x0a\x09<pa\
th class=\x22st4\x22 d\
=\x22M165.66,241.62\
l299.45-3.21c5.0\
8-0.05,11.88,2.3\
4,14.89,6.42l3.8\
5,2.93c5.52,7.49\
,5.06,22.81-1.12\
,29.77\x0a\x09\x09l-1.1,1\
.24c-5.9,6.65-14\
.37,10.46-23.26,\
10.47l-282.44,0.\
19c-10.96,0.01-2\
1.06-5.97-26.31-\
15.59l0,0\x0a\x09\x09c-4.\
06-7.42-3.79-16.\
46,0.71-23.63v0C\
153.65,244.92,15\
9.42,241.69,165.\
66,241.62z\x22/>\x0a\x09<\
path class=\x22st7\x22\
 d=\x22M247.54,330.\
03l-38.9,0.04c-1\
2.32,0.01-22.31,\
8.66-22.35,19.35\
l-0.19,47.14\x0a\x09\x09c\
-0.04,10.28,9.58\
,18.62,21.43,18.\
59l41.46-0.11c0,\
0,0.47-27.86-0.4\
9-49.02C247.85,3\
51.58,245.59,330\
.43,247.54,330.0\
3z\x22/>\x0a\x09<path cla\
ss=\x22st4\x22 d=\x22M228\
.27,48.7l-41.52-\
9.72c-10.96-2.56\
-22.49-0.4-31.77\
,5.96l-3.95,2.7c\
-10.27,7.04-10.9\
2,17.25-12.17,29\
.64\x0a\x09\x09l-0.78,32.\
53l1.01,106.85c0\
.12,13.28,3.29,2\
5.77,16.55,25.05\
l71.61-3.87c7.62\
-0.41,13.61-6.68\
,13.68-14.31l1.4\
5-156.87\x0a\x09\x09C242.\
48,58.12,236.61,\
50.65,228.27,48.\
7z\x22/>\x0a\x09<path cla\
ss=\x22st8\x22 d=\x22M138\
.47,93.87l103.66\
,1.04L138.47,93.\
87z\x22/>\x0a\x09<path cl\
ass=\x22st4\x22 d=\x22M21\
5.43,289.4l10.94\
,16.23c8.21,15.3\
9,12.87,32.42,13\
.62,49.84l1.7,39\
.13c0.47,10.73-1\
,21.45-4.33,31.6\
5\x0a\x09\x09l-12.39,27.4\
c-4.13,12.67,13.\
34,21.25,26.67,2\
1.19h184.3c8.51-\
0.03,21.93-16.42\
,17.92-23.93l-30\
.74-50.42\x0a\x09\x09c-4.\
4-8.24-2.03-18.4\
6,5.54-23.92l0,0\
c8.99-6.48,16.12\
-15.21,20.68-25.\
32l5.09-11.28c5.\
11-11.32,8.01-23\
.5,8.57-35.9l0.6\
5-14.64\x0a\x09\x09L215.4\
3,289.4z\x22/>\x0a\x09<pa\
th class=\x22st8\x22 d\
=\x22M429.83,375.71\
c0,0-16.43,12.35\
-38.28,15.81c-6.\
09,0.96-29.42,0.\
69-29.42,0.69\x22/>\
\x0a</g>\x0a<g id=\x22Lay\
er_3\x22>\x0a</g>\x0a<g i\
d=\x22Layer_5\x22>\x0a\x09<g\
 id=\x22Layer_4\x22>\x0a\x09\
</g>\x0a</g>\x0a<g id=\
\x22Layer_6\x22>\x0a</g>\x0a\
<g id=\x22Layer_7\x22>\
\x0a</g>\x0a</svg>\x0a\
\x00\x00\x01g\
<\
svg xmlns=\x22http:\
//www.w3.org/200\
0/svg\x22 width=\x2232\
\x22 height=\x2232\x22 vi\
ewBox=\x220 0 24 24\
\x22><path fill=\x22no\
ne\x22 stroke=\x22#fff\
fff\x22 stroke-line\
cap=\x22round\x22 stro\
ke-linejoin=\x22rou\
nd\x22 stroke-width\
=\x221.5\x22 d=\x22M18 8.\
4c0-1.697-.632-3\
.325-1.757-4.525\
S13.59 2 12 2s-3\
.117.674-4.243 1\
.875C6.632 5.075\
 6 6.703 6 8.4C6\
 15.867 3 18 3 1\
8h18s-3-2.133-3-\
9.6M13.73 21a2 2\
 0 0 1-3.46 0\x22/>\
</svg>\
\x00\x00\x01\xa1\
<\
svg xmlns=\x22http:\
//www.w3.org/200\
0/svg\x22 width=\x2232\
\x22 height=\x2232\x22 vi\
ewBox=\x220 0 30 30\
\x22><path fill=\x22#f\
fffff\x22 d=\x22M9.81 \
15.25c0 .92.23 1\
.78.7 2.57s1.1 1\
.43 1.9 1.9s1.66\
.71 2.59.71s1.8-\
.24 2.61-.71a5.3\
 5.3 0 0 0 1.92-\
1.9c.47-.8.71-1.\
65.71-2.57c0-.6-\
.17-1.31-.52-2.1\
4s-.77-1.6-1.26-\
2.3c-.44-.57-.96\
-1.2-1.56-1.88s-\
1.65-1.73-1.89-1\
.97l-1.28 1.29c-\
.62.6-1.22 1.29-\
1.79 2.08s-1.07 \
1.64-1.49 2.55c-\
.44.91-.64 1.7-.\
64 2.37\x22/></svg>\
\
\x00\x00\x02\x82\
<\
svg xmlns=\x22http:\
//www.w3.org/200\
0/svg\x22 width=\x2232\
\x22 height=\x2232\x22 vi\
ewBox=\x220 0 24 24\
\x22><g fill=\x22none\x22\
 stroke=\x22#ffffff\
\x22 stroke-linecap\
=\x22round\x22 stroke-\
linejoin=\x22round\x22\
 stroke-width=\x221\
.5\x22 color=\x22#ffff\
ff\x22><path d=\x22M12\
 16a5 5 0 1 1-10\
 0a5 5 0 0 1 10 \
0m6 3.5a1.5 1.5 \
0 1 1-3 0a1.5 1.\
5 0 0 1 3 0M7.00\
8 16h-.009\x22/><pa\
th d=\x22m6 11l-.62\
8-5.023c-.145-1.\
159-.217-1.738-.\
522-2.155a2 2 0 \
0 0-.647-.572C3.\
751 3 3.167 3 2 \
3m4 4h5.5c2.357 \
0 3.536 0 4.268.\
732S16.5 9.643 1\
6.5 12v6\x22/><path\
 d=\x22M12 14h4.024\
c.885 0 1.328 0 \
1.713.189q.14.06\
8.267.158c.356.2\
5.601.659 1.092 \
1.474c.393.653.5\
9.98.884 1.107q.\
105.044.215.063c\
.312.052.629-.12\
4 1.263-.475l.54\
2-.3\x22/></g></svg\
>\
\x00\x00\x03\x93\
<\
svg xmlns=\x22http:\
//www.w3.org/200\
0/svg\x22 width=\x2232\
\x22 height=\x2232\x22 vi\
ewBox=\x220 0 20 20\
\x22><!-- Icon from\
 Pepicons Pencil\
 by CyCraft - ht\
tps://github.com\
/CyCraft/pepicon\
s/blob/dev/LICEN\
SE --><g fill=\x22#\
ffffff\x22 fill-rul\
e=\x22evenodd\x22 clip\
-rule=\x22evenodd\x22>\
<path d=\x22M5 9a2 \
2 0 1 0 0-4a2 2 \
0 0 0 0 4m0 1a3 \
3 0 1 0 0-6a3 3 \
0 0 0 0 6\x22/><pat\
h d=\x22M3.854 8.89\
6a.5.5 0 0 1 0 .\
708l-.338.337A3.\
47 3.47 0 0 0 2.\
5 12.394v1.856a.\
5.5 0 1 1-1 0v-1\
.856a4.47 4.47 0\
 0 1 1.309-3.16l\
.337-.338a.5.5 0\
 0 1 .708 0m11.7\
92-.3a.5.5 0 0 0\
 0 .708l.338.337\
A3.47 3.47 0 0 1\
 17 12.094v2.156\
a.5.5 0 0 0 1 0v\
-2.156a4.47 4.47\
 0 0 0-1.309-3.1\
6l-.337-.338a.5.\
5 0 0 0-.708 0\x22/\
><path d=\x22M14 9a\
2 2 0 1 1 0-4a2 \
2 0 0 1 0 4m0 1a\
3 3 0 1 1 0-6a3 \
3 0 0 1 0 6m-4.5\
 3.25a2.5 2.5 0 \
0 0-2.5 2.5v1.3a\
.5.5 0 0 1-1 0v-\
1.3a3.5 3.5 0 0 \
1 7 0v1.3a.5.5 0\
 1 1-1 0v-1.3a2.\
5 2.5 0 0 0-2.5-\
2.5\x22/><path d=\x22M\
9.5 11.75a2 2 0 \
1 0 0-4a2 2 0 0 \
0 0 4m0 1a3 3 0 \
1 0 0-6a3 3 0 0 \
0 0 6\x22/></g></sv\
g>\
\x00\x00\x01u\
<\
svg xmlns=\x22http:\
//www.w3.org/200\
0/svg\x22 width=\x2232\
\x22 height=\x2232\x22 vi\
ewBox=\x220 0 24 24\
\x22><!-- Icon from\
 Huge Icons by H\
ugeicons - undef\
ined --><g fill=\
\x22none\x22 stroke=\x22#\
ffffff\x22 stroke-l\
inecap=\x22round\x22 s\
troke-linejoin=\x22\
round\x22 stroke-wi\
dth=\x221.5\x22 color=\
\x22#ffffff\x22><circl\
e cx=\x2212\x22 cy=\x2212\
\x22 r=\x2210\x22/><path \
d=\x22M16 12H8m8 0c\
0 .7-1.994 2.008\
-2.5 2.5M16 12c0\
-.7-1.994-2.008-\
2.5-2.5\x22/></g></\
svg>\
\x00\x00\x1e\xfe\
<\
?xml version=\x221.\
0\x22 encoding=\x22utf\
-8\x22?>\x0a<!-- Gener\
ator: Adobe Adob\
e Illustrator 24\
.2.0, SVG Export\
 Plug-In . SVG V\
ersion: 6.00 Bui\
ld 0)  -->\x0a<svg \
version=\x221.1\x22 xm\
lns=\x22http://www.\
w3.org/2000/svg\x22\
 xmlns:xlink=\x22ht\
tp://www.w3.org/\
1999/xlink\x22 x=\x220\
px\x22 y=\x220px\x22\x0a\x09 wi\
dth=\x22595.28px\x22 h\
eight=\x22570.62px\x22\
 viewBox=\x220 0 59\
5.28 570.62\x22 sty\
le=\x22enable-backg\
round:new 0 0 59\
5.28 570.62;\x22\x0a\x09 \
xml:space=\x22prese\
rve\x22>\x0a<style typ\
e=\x22text/css\x22>\x0a\x09.\
st0{fill:#F4BAA6\
;stroke:#F4BAA6;\
stroke-width:5;s\
troke-miterlimit\
:10;}\x0a\x09.st1{disp\
lay:none;}\x0a\x09.st2\
{fill:#F4BAA6;st\
roke:#DB9E8A;str\
oke-width:5;stro\
ke-miterlimit:10\
;}\x0a\x09.st3{display\
:none;fill:#29AB\
E2;stroke:#00000\
0;stroke-width:5\
;stroke-miterlim\
it:10;}\x0a\x09.st4{fi\
ll:#E6E6E6;strok\
e:#E6E6E6;stroke\
-width:5;stroke-\
miterlimit:10;}\x0a\
\x09.st5{fill:#92CE\
E8;stroke:#92CEE\
8;stroke-width:5\
;stroke-miterlim\
it:10;}\x0a\x09.st6{fi\
ll:#29ABE2;strok\
e:#29ABE2;stroke\
-width:5;stroke-\
miterlimit:10;}\x0a\
\x09.st7{fill:#B3B3\
B3;stroke:#B3B3B\
3;stroke-width:5\
;stroke-miterlim\
it:10;}\x0a\x09.st8{fi\
ll:#E6E6E6;strok\
e:#D9D9D9;stroke\
-width:5;stroke-\
miterlimit:10;}\x0a\
\x09.st9{fill:#E6E6\
E6;stroke:#B3B3B\
3;stroke-width:5\
;stroke-miterlim\
it:10;}\x0a\x09.st10{f\
ill:#C48F7E;}\x0a\x09.\
st11{fill:#E6B5A\
5;}\x0a\x09.st12{fill:\
#F4BAA6;}\x0a\x09.st13\
{fill:#EDC1B2;}\x0a\
\x09.st14{fill:#F4B\
AA6;stroke:#F4BA\
A6;stroke-miterl\
imit:10;}\x0a\x09.st15\
{fill:#FF6B89;st\
roke:#FF6B89;str\
oke-miterlimit:1\
0;}\x0a\x09.st16{fill:\
none;stroke:#8A8\
A8A;stroke-width\
:5;stroke-miterl\
imit:10;}\x0a\x09.st17\
{fill:#92CEE8;}\x0a\
\x09.st18{fill:#F5F\
5F5;}\x0a\x09.st19{fil\
l:none;stroke:#9\
2CEE8;stroke-wid\
th:5;stroke-mite\
rlimit:10;}\x0a\x09.st\
20{fill:#855B4E;\
}\x0a\x09.st21{fill:#A\
37364;}\x0a\x09.st22{f\
ill:#EBCE42;}\x0a\x09.\
st23{fill:#94949\
4;stroke:#949494\
;stroke-width:5;\
stroke-miterlimi\
t:10;}\x0a\x09.st24{st\
roke:#000000;str\
oke-miterlimit:1\
0;}\x0a\x09.st25{fill:\
#F5F5F5;stroke:#\
F5F5F5;stroke-wi\
dth:5;stroke-mit\
erlimit:10;}\x0a\x09.s\
t26{fill:#FFFFFF\
;}\x0a\x09.st27{fill:#\
A37364;stroke:#A\
37364;stroke-wid\
th:5;stroke-mite\
rlimit:10;}\x0a\x09.st\
28{fill:#A37364;\
stroke:#A37364;s\
troke-width:3;st\
roke-miterlimit:\
10;}\x0a\x09.st29{fill\
:#6B9DB3;stroke:\
#6B9DB3;stroke-w\
idth:5;stroke-mi\
terlimit:10;}\x0a\x09.\
st30{fill:#DB9E8\
A;stroke:#346C85\
;stroke-width:5;\
stroke-miterlimi\
t:10;}\x0a\x09.st31{fi\
ll:#346C85;strok\
e:#346C85;stroke\
-width:5;stroke-\
miterlimit:10;}\x0a\
\x09.st32{fill:#2A6\
27A;stroke:#2A62\
7A;stroke-width:\
5;stroke-miterli\
mit:10;}\x0a\x09.st33{\
fill:#6B9DB3;}\x0a\x09\
.st34{fill:#EDED\
ED;}\x0a\x09.st35{fill\
:none;stroke:#32\
3E9C;stroke-widt\
h:7;stroke-miter\
limit:10;}\x0a\x09.st3\
6{fill:#C23A4E;}\
\x0a\x09.st37{fill:#C2\
3A4E;stroke:#C23\
A4E;stroke-miter\
limit:10;}\x0a\x09.st3\
8{fill:#C23A4E;s\
troke:#C23A4E;st\
roke-width:5;str\
oke-miterlimit:1\
0;}\x0a\x09.st39{fill:\
#8A8A8A;stroke:#\
323E9C;stroke-wi\
dth:7;stroke-mit\
erlimit:10;}\x0a\x09.s\
t40{fill:#323E9C\
;stroke:#323E9C;\
stroke-miterlimi\
t:10;}\x0a\x09.st41{fi\
ll:#79C77F;}\x0a\x09.s\
t42{opacity:0.72\
94;fill:#8DB9CC;\
}\x0a\x09.st43{fill:#D\
B9E8A;stroke:#DB\
9E8A;stroke-mite\
rlimit:10;}\x0a\x09.st\
44{opacity:0.588\
2;fill:#FFFF00;}\
\x0a\x09.st45{fill:#8C\
C63F;stroke:#8CC\
63F;stroke-miter\
limit:10;}\x0a\x09.st4\
6{fill:#FF0000;}\
\x0a\x09.st47{fill:#C1\
272D;}\x0a\x09.st48{fi\
ll:#8CC63F;strok\
e:#80B53A;stroke\
-miterlimit:10;}\
\x0a\x09.st49{opacity:\
0.9608;fill:#FF0\
000;}\x0a\x09.st50{opa\
city:0.949;fill:\
#C1272D;}\x0a\x09.st51\
{fill:#FFFD7A;st\
roke:#FFFD7A;str\
oke-miterlimit:1\
0;}\x0a\x09.st52{fill:\
#8CC63F;}\x0a\x09.st53\
{fill:#B38576;st\
roke:#B38576;str\
oke-miterlimit:1\
0;}\x0a\x09.st54{opaci\
ty:0.7412;fill:#\
9E68A3;stroke:#9\
E68A3;stroke-mit\
erlimit:10;}\x0a\x09.s\
t55{opacity:0.50\
2;stroke:#000000\
;stroke-miterlim\
it:10;}\x0a\x09.st56{f\
ill:#C48F7E;stro\
ke:#C48F7E;strok\
e-miterlimit:10;\
}\x0a\x09.st57{fill:#8\
55B4E;stroke:#85\
5B4E;stroke-mite\
rlimit:10;}\x0a\x09.st\
58{opacity:0.670\
6;fill:#F15A24;}\
\x0a\x09.st59{fill:#9E\
005D;}\x0a\x09.st60{op\
acity:0.6784;fil\
l:#FFFFFF;stroke\
:#FFFFFF;stroke-\
miterlimit:10;}\x0a\
\x09.st61{opacity:0\
.6588;fill:#FFFD\
7A;stroke:#FFFD7\
A;stroke-miterli\
mit:10;}\x0a\x09.st62{\
fill:#949494;str\
oke:#949494;stro\
ke-miterlimit:10\
;}\x0a\x09.st63{fill:n\
one;stroke:#9494\
94;stroke-width:\
3;stroke-miterli\
mit:10;}\x0a\x09.st64{\
fill:#FFFD7A;str\
oke:#EDEB77;stro\
ke-miterlimit:10\
;}\x0a\x09.st65{fill:#\
FF9191;stroke:#F\
F9191;stroke-mit\
erlimit:10;}\x0a\x09.s\
t66{fill:#FFFFFF\
;stroke:#FFFFFF;\
stroke-miterlimi\
t:10;}\x0a</style>\x0a\
<g id=\x22Layer_1\x22>\
\x0a</g>\x0a<g id=\x22Lay\
er_2\x22>\x0a</g>\x0a<g i\
d=\x22Layer_3\x22>\x0a</g\
>\x0a<g id=\x22Layer_5\
\x22>\x0a\x09<path class=\
\x22st23\x22 d=\x22M219.3\
5,248.94l-41.4,0\
.89l2.19-9.07c2.\
98-12.74,18.13-2\
5.21,30.67-28.83\
c16.13-4.66,31.2\
7,2.36,45.6,11.1\
7\x0a\x09\x09l-37.31,26.4\
4\x22/>\x0a\x09<g id=\x22Lay\
er_4\x22>\x0a\x09\x09<path c\
lass=\x22st24\x22 d=\x22M\
209.19,80.09l23.\
97-0.24c4.26-0.0\
4,7.62,3.61,7.22\
,7.85v0c-0.12,1.\
24-0.54,2.43-1.2\
4,3.46l-18.11,26\
.77\x0a\x09\x09\x09c-1.34,1.\
98,0.06,4.65,2.4\
5,4.68l12.95,0.1\
3c2.9,0.03,5.26,\
2.35,5.33,5.26l0\
.03,1.36c0.04,1.\
67-1.29,3.05-2.9\
6,3.07l-32.58,0.\
43\x0a\x09\x09\x09c-1.69,0.0\
2-3.06-1.35-3.04\
-3.04l0.06-4.74c\
0.02-1.69,0.56-3\
.34,1.54-4.72l17\
.89-25.26c1.41-1\
.99-0.02-4.74-2.\
46-4.73L205.8,90\
.4\x0a\x09\x09\x09c-1.68,0-3\
.04-1.37-3.01-3.\
05l0.02-0.92C202\
.87,82.93,205.7,\
80.13,209.19,80.\
09z\x22/>\x0a\x09\x09<path c\
lass=\x22st24\x22 d=\x22M\
252.67,134.57l19\
.05-0.2c3.39-0.0\
4,6.06,3.03,5.74\
,6.6v0c-0.09,1.0\
4-0.43,2.04-0.98\
,2.91l-14.4,22.5\
1\x0a\x09\x09\x09c-1.06,1.66\
,0.05,3.91,1.95,\
3.93l10.29,0.11c\
2.31,0.02,4.18,1\
.98,4.24,4.42l0.\
03,1.14c0.03,1.4\
-1.03,2.56-2.35,\
2.58l-25.89,0.37\
\x0a\x09\x09\x09c-1.34,0.02-\
2.43-1.13-2.42-2\
.55l0.05-3.98c0.\
02-1.42,0.44-2.8\
1,1.22-3.97l14.2\
2-21.24c1.12-1.6\
7-0.01-3.98-1.95\
-3.98l-11.49,0.0\
3\x0a\x09\x09\x09c-1.34,0-2.\
41-1.15-2.39-2.5\
6l0.01-0.78C247.\
65,136.96,249.9,\
134.6,252.67,134\
.57z\x22/>\x0a\x09\x09<path \
class=\x22st25\x22 d=\x22\
M222.3,248l-13.2\
1,0.05c-28.68,0.\
12-56.9,7.12-82.\
31,20.43l-20.24,\
10.6l29.33,22.91\
\x0a\x09\x09\x09c14.34,11.2,\
31.92,17.43,50.1\
1,17.76l33.88,0.\
62L222.3,248z\x22/>\
\x0a\x09\x09<polygon clas\
s=\x22st25\x22 points=\
\x22133.14,317.92 2\
17.18,317.18 267\
.76,337.75 133.8\
2,339.33 \x09\x09\x22/>\x0a\x09\
</g>\x0a\x09<path clas\
s=\x22st26\x22 d=\x22M95.\
86,176.74h20.01c\
8.32,0,15.1,6.67\
,15.23,14.99l3.9\
6,245.25c-0.05,1\
3.68-11.15,24.75\
-24.84,24.75h-7.\
06\x0a\x09\x09c-14.01,0-2\
5.41-11.28-25.56\
-25.29l-2.54-238\
.66C74.93,186.2,\
84.28,176.74,95.\
86,176.74z\x22/>\x0a\x09<\
path class=\x22st27\
\x22 d=\x22M101.44,160\
.01h20.01c8.32,0\
,15.1,6.67,15.23\
,14.99l3.96,245.\
25C140.59,433.93\
,129.48,445,115.\
8,445h-7.06\x0a\x09\x09c-\
14.01,0-25.41-11\
.28-25.56-25.29l\
-2.54-238.66C80.\
5,169.47,89.86,1\
60.01,101.44,160\
.01z\x22/>\x0a\x09<polygo\
n class=\x22st28\x22 p\
oints=\x22135.06,34\
0.31 272.22,338.\
24 380.73,386.12\
 455.2,337.75 45\
5.2,423.01 135.0\
6,421.98 \x09\x22/>\x0a\x09<\
circle class=\x22st\
29\x22 cx=\x22404.87\x22 \
cy=\x22137.43\x22 r=\x228\
9.75\x22/>\x0a\x09<line c\
lass=\x22st30\x22 x1=\x22\
477.8\x22 y1=\x22188.0\
4\x22 x2=\x22467.1\x22 y2\
=\x22179.04\x22/>\x0a\x09<pa\
th class=\x22st31\x22 \
d=\x22M357.95,143.4\
2l0.03-2.4c0.08-\
6.14,5.79-11.09,\
12.82-11.11l34.9\
3-0.08c6.84-0.02\
,12.39,4.83,12.3\
9,10.81v6.04\x0a\x09\x09c\
-3.53,6.48-5.16,\
10-11.48,9.95l-3\
4.23-0.29C364.33\
,156.28,357.85,1\
50.49,357.95,143\
.42z\x22/>\x0a\x09<path c\
lass=\x22st32\x22 d=\x22M\
404.59,89.8l1.1,\
0.05c7.12,0.3,12\
.78,7.45,12.81,1\
6.19l0.12,35.56c\
0.03,8.99-5.93,1\
6.29-13.26,16.25\
h0\x0a\x09\x09c-7.9-0.05-\
14.28-7.94-14.24\
-17.63l0.14-34.6\
9C391.3,96.61,39\
7.33,89.5,404.59\
,89.8z\x22/>\x0a\x09<line\
 class=\x22st30\x22 x1\
=\x22360.06\x22 y1=\x2221\
4.67\x22 x2=\x22367.62\
\x22 y2=\x22197.54\x22/>\x0a\
\x09<line class=\x22st\
30\x22 x1=\x22403.78\x22 \
y1=\x2248\x22 x2=\x22403.\
55\x22 y2=\x2275.3\x22/>\x0a\
\x09<line class=\x22st\
30\x22 x1=\x22493.37\x22 \
y1=\x22142.91\x22 x2=\x22\
462.77\x22 y2=\x22142.\
63\x22/>\x0a\x09<line cla\
ss=\x22st30\x22 x1=\x2231\
4.84\x22 y1=\x22138.34\
\x22 x2=\x22348.26\x22 y2\
=\x22137.54\x22/>\x0a\x09<pa\
th class=\x22st4\x22 d\
=\x22M454.01,336.45\
l-73.28,49.67l-1\
70.41-74.46l3.21\
-31.53l3.92-22.8\
1c0.94-5.07,7.78\
-17.21,18.19-24.\
54\x0a\x09\x09c10.47-7.37\
,24.53-9.91,29.7\
1-9.63l0.55-0.18\
c10.13-1.21,31.2\
6-1.17,41.39,0.1\
1l38.68,4.08c15.\
26,1.11,61.67,22\
.35,75.26,29.39\x0a\
\x09\x09l34.74,25.32L4\
54.01,336.45z\x22/>\
\x0a\x09<line class=\x22s\
t30\x22 x1=\x22403.74\x22\
 y1=\x22228.52\x22 x2=\
\x22404.38\x22 y2=\x22194\
.78\x22/>\x0a\x09<path cl\
ass=\x22st27\x22 d=\x22M4\
76.12,251.71l14.\
57,0.01c11.46,0.\
01,20.74,9.3,20.\
74,20.76v145.94c\
0,14.85-12.04,26\
.9-26.9,26.9h-4.\
91\x0a\x09\x09c-13.22,0-2\
3.87-10.82-23.67\
-24.04l2.38-152.\
07C458.5,259.5,4\
66.41,251.71,476\
.12,251.71z\x22/>\x0a\x09\
<line class=\x22st3\
0\x22 x1=\x22360.92\x22 y\
1=\x2262.18\x22 x2=\x2237\
0.13\x22 y2=\x2279.85\x22\
/>\x0a\x09<line class=\
\x22st30\x22 x1=\x22329.9\
7\x22 y1=\x2289.79\x22 x2\
=\x22344.22\x22 y2=\x2210\
1.9\x22/>\x0a\x09<line cl\
ass=\x22st30\x22 x1=\x223\
28.68\x22 y1=\x22183.2\
2\x22 x2=\x22345.5\x22 y2\
=\x22170.26\x22/>\x0a\x09<li\
ne class=\x22st31\x22 \
x1=\x22452.49\x22 y1=\x22\
213.34\x22 x2=\x22444.\
52\x22 y2=\x22199.49\x22/\
>\x0a\x09<line class=\x22\
st30\x22 x1=\x22450.96\
\x22 y1=\x2263.04\x22 x2=\
\x22440.1\x22 y2=\x2276.8\
\x22/>\x0a\x09<line class\
=\x22st30\x22 x1=\x22485.\
27\x22 y1=\x22100.07\x22 \
x2=\x22469.65\x22 y2=\x22\
104.31\x22/>\x0a\x09<path\
 class=\x22st25\x22 d=\
\x22M298.17,223.99c\
-0.47-0.74,0.05-\
1.71,0.92-1.73l1\
3.19-0.38c31.19-\
1.14,62.03,6.79,\
88.8,22.83l15.32\
,9.17\x0a\x09\x09c1.9,1.1\
4,2.04,3.84,0.27\
,5.17l-65.18,48.\
88L298.17,223.99\
z\x22/>\x0a</g>\x0a<g id=\
\x22Layer_6\x22>\x0a</g>\x0a\
<g id=\x22Layer_7\x22>\
\x0a</g>\x0a</svg>\x0a\
\x00\x00\x01\x1f\
<\
svg xmlns=\x22http:\
//www.w3.org/200\
0/svg\x22 width=\x2232\
\x22 height=\x2232\x22 vi\
ewBox=\x220 0 24 24\
\x22><path fill=\x22no\
ne\x22 stroke=\x22#fff\
fff\x22 stroke-line\
cap=\x22round\x22 stro\
ke-linejoin=\x22rou\
nd\x22 stroke-width\
=\x221.5\x22 d=\x22M11.47\
5 2.947a.6.6 0 0\
 1 1.05 0l9.373 \
16.912a.6.6 0 0 \
1-.524.891H2.626\
a.6.6 0 0 1-.525\
-.89z\x22/></svg>\
\x00\x00\x00\xe2\
<\
svg xmlns=\x22http:\
//www.w3.org/200\
0/svg\x22 width=\x2232\
\x22 height=\x2232\x22 vi\
ewBox=\x220 0 24 24\
\x22><path fill=\x22no\
ne\x22 stroke=\x22#fff\
fff\x22 stroke-line\
cap=\x22round\x22 stro\
ke-linejoin=\x22rou\
nd\x22 stroke-width\
=\x221.5\x22 d=\x22M19 6L\
6 19m0 0V6.52M6 \
19h12.48\x22/></svg\
>\
\x00\x00\x01\x1a\
<\
svg xmlns=\x22http:\
//www.w3.org/200\
0/svg\x22 width=\x2232\
\x22 height=\x2232\x22 vi\
ewBox=\x220 0 24 24\
\x22><path fill=\x22no\
ne\x22 stroke=\x22#fff\
fff\x22 stroke-line\
cap=\x22round\x22 stro\
ke-linejoin=\x22rou\
nd\x22 stroke-width\
=\x221.5\x22 d=\x22M9 9L4\
 4m0 0v4m0-4h4m7\
 5l5-5m0 0v4m0-4\
h-4M9 15l-5 5m0 \
0v-4m0 4h4m7-5l5\
 5m0 0v-4m0 4h-4\
\x22/></svg>\
\x00\x00\x00\xdb\
<\
svg xmlns=\x22http:\
//www.w3.org/200\
0/svg\x22 width=\x2232\
\x22 height=\x2232\x22 vi\
ewBox=\x220 0 24 24\
\x22><path fill=\x22no\
ne\x22 stroke=\x22#fff\
fff\x22 stroke-line\
cap=\x22round\x22 stro\
ke-linejoin=\x22rou\
nd\x22 stroke-width\
=\x221.5\x22 d=\x22M3 5h1\
8M3 12h18M3 19h1\
8\x22/></svg>\
\x00\x00\x1d=\
<\
?xml version=\x221.\
0\x22 encoding=\x22utf\
-8\x22?>\x0a<!-- Gener\
ator: Adobe Adob\
e Illustrator 24\
.2.0, SVG Export\
 Plug-In . SVG V\
ersion: 6.00 Bui\
ld 0)  -->\x0a<svg \
version=\x221.1\x22 xm\
lns=\x22http://www.\
w3.org/2000/svg\x22\
 xmlns:xlink=\x22ht\
tp://www.w3.org/\
1999/xlink\x22 x=\x220\
px\x22 y=\x220px\x22\x0a\x09 wi\
dth=\x22595.28px\x22 h\
eight=\x22560.42px\x22\
 viewBox=\x220 0 59\
5.28 560.42\x22 sty\
le=\x22enable-backg\
round:new 0 0 59\
5.28 560.42;\x22\x0a\x09 \
xml:space=\x22prese\
rve\x22>\x0a<style typ\
e=\x22text/css\x22>\x0a\x09.\
st0{fill:#F4BAA6\
;stroke:#F4BAA6;\
stroke-width:5;s\
troke-miterlimit\
:10;}\x0a\x09.st1{disp\
lay:none;}\x0a\x09.st2\
{fill:#F4BAA6;st\
roke:#DB9E8A;str\
oke-width:5;stro\
ke-miterlimit:10\
;}\x0a\x09.st3{display\
:none;fill:#29AB\
E2;stroke:#00000\
0;stroke-width:5\
;stroke-miterlim\
it:10;}\x0a\x09.st4{fi\
ll:#E6E6E6;strok\
e:#E6E6E6;stroke\
-width:5;stroke-\
miterlimit:10;}\x0a\
\x09.st5{fill:#92CE\
E8;stroke:#92CEE\
8;stroke-width:5\
;stroke-miterlim\
it:10;}\x0a\x09.st6{fi\
ll:#29ABE2;strok\
e:#29ABE2;stroke\
-width:5;stroke-\
miterlimit:10;}\x0a\
\x09.st7{fill:#B3B3\
B3;stroke:#B3B3B\
3;stroke-width:5\
;stroke-miterlim\
it:10;}\x0a\x09.st8{fi\
ll:#E6E6E6;strok\
e:#D9D9D9;stroke\
-width:5;stroke-\
miterlimit:10;}\x0a\
\x09.st9{fill:#E6E6\
E6;stroke:#B3B3B\
3;stroke-width:5\
;stroke-miterlim\
it:10;}\x0a\x09.st10{f\
ill:#C48F7E;}\x0a\x09.\
st11{fill:#E6B5A\
5;}\x0a\x09.st12{fill:\
#F4BAA6;}\x0a\x09.st13\
{fill:#EDC1B2;}\x0a\
\x09.st14{fill:#F4B\
AA6;stroke:#F4BA\
A6;stroke-miterl\
imit:10;}\x0a\x09.st15\
{fill:#FF6B89;st\
roke:#FF6B89;str\
oke-miterlimit:1\
0;}\x0a\x09.st16{fill:\
none;stroke:#8A8\
A8A;stroke-width\
:5;stroke-miterl\
imit:10;}\x0a\x09.st17\
{fill:#92CEE8;}\x0a\
\x09.st18{fill:#F5F\
5F5;}\x0a\x09.st19{fil\
l:none;stroke:#9\
2CEE8;stroke-wid\
th:5;stroke-mite\
rlimit:10;}\x0a\x09.st\
20{fill:#855B4E;\
}\x0a\x09.st21{fill:#A\
37364;}\x0a\x09.st22{f\
ill:#EBCE42;}\x0a\x09.\
st23{fill:#94949\
4;stroke:#949494\
;stroke-width:5;\
stroke-miterlimi\
t:10;}\x0a\x09.st24{st\
roke:#000000;str\
oke-miterlimit:1\
0;}\x0a\x09.st25{fill:\
#F5F5F5;stroke:#\
F5F5F5;stroke-wi\
dth:5;stroke-mit\
erlimit:10;}\x0a\x09.s\
t26{fill:#FFFFFF\
;}\x0a\x09.st27{fill:#\
A37364;stroke:#A\
37364;stroke-wid\
th:5;stroke-mite\
rlimit:10;}\x0a\x09.st\
28{fill:#A37364;\
stroke:#A37364;s\
troke-width:3;st\
roke-miterlimit:\
10;}\x0a\x09.st29{fill\
:#6B9DB3;stroke:\
#6B9DB3;stroke-w\
idth:5;stroke-mi\
terlimit:10;}\x0a\x09.\
st30{fill:#DB9E8\
A;stroke:#346C85\
;stroke-width:5;\
stroke-miterlimi\
t:10;}\x0a\x09.st31{fi\
ll:#346C85;strok\
e:#346C85;stroke\
-width:5;stroke-\
miterlimit:10;}\x0a\
\x09.st32{fill:#2A6\
27A;stroke:#2A62\
7A;stroke-width:\
5;stroke-miterli\
mit:10;}\x0a\x09.st33{\
fill:#6B9DB3;}\x0a\x09\
.st34{fill:#EDED\
ED;}\x0a\x09.st35{fill\
:none;stroke:#32\
3E9C;stroke-widt\
h:7;stroke-miter\
limit:10;}\x0a\x09.st3\
6{fill:#C23A4E;}\
\x0a\x09.st37{fill:#C2\
3A4E;stroke:#C23\
A4E;stroke-miter\
limit:10;}\x0a\x09.st3\
8{fill:#C23A4E;s\
troke:#C23A4E;st\
roke-width:5;str\
oke-miterlimit:1\
0;}\x0a\x09.st39{fill:\
#8A8A8A;stroke:#\
323E9C;stroke-wi\
dth:7;stroke-mit\
erlimit:10;}\x0a\x09.s\
t40{fill:#323E9C\
;stroke:#323E9C;\
stroke-miterlimi\
t:10;}\x0a\x09.st41{fi\
ll:#79C77F;}\x0a\x09.s\
t42{opacity:0.72\
94;fill:#8DB9CC;\
}\x0a\x09.st43{fill:#D\
B9E8A;stroke:#DB\
9E8A;stroke-mite\
rlimit:10;}\x0a\x09.st\
44{opacity:0.588\
2;fill:#FFFF00;}\
\x0a\x09.st45{fill:#8C\
C63F;stroke:#8CC\
63F;stroke-miter\
limit:10;}\x0a\x09.st4\
6{fill:#FF0000;}\
\x0a\x09.st47{fill:#C1\
272D;}\x0a\x09.st48{fi\
ll:#8CC63F;strok\
e:#80B53A;stroke\
-miterlimit:10;}\
\x0a\x09.st49{opacity:\
0.9608;fill:#FF0\
000;}\x0a\x09.st50{opa\
city:0.949;fill:\
#C1272D;}\x0a\x09.st51\
{fill:#FFFD7A;st\
roke:#FFFD7A;str\
oke-miterlimit:1\
0;}\x0a\x09.st52{fill:\
#8CC63F;}\x0a\x09.st53\
{fill:#B38576;st\
roke:#B38576;str\
oke-miterlimit:1\
0;}\x0a\x09.st54{opaci\
ty:0.7412;fill:#\
9E68A3;stroke:#9\
E68A3;stroke-mit\
erlimit:10;}\x0a\x09.s\
t55{opacity:0.50\
2;stroke:#000000\
;stroke-miterlim\
it:10;}\x0a\x09.st56{f\
ill:#C48F7E;stro\
ke:#C48F7E;strok\
e-miterlimit:10;\
}\x0a\x09.st57{fill:#8\
55B4E;stroke:#85\
5B4E;stroke-mite\
rlimit:10;}\x0a\x09.st\
58{opacity:0.670\
6;fill:#F15A24;}\
\x0a\x09.st59{fill:#9E\
005D;}\x0a\x09.st60{op\
acity:0.6784;fil\
l:#FFFFFF;stroke\
:#FFFFFF;stroke-\
miterlimit:10;}\x0a\
\x09.st61{opacity:0\
.6588;fill:#FFFD\
7A;stroke:#FFFD7\
A;stroke-miterli\
mit:10;}\x0a\x09.st62{\
fill:#949494;str\
oke:#949494;stro\
ke-miterlimit:10\
;}\x0a\x09.st63{fill:n\
one;stroke:#9494\
94;stroke-width:\
3;stroke-miterli\
mit:10;}\x0a\x09.st64{\
fill:#FFFD7A;str\
oke:#EDEB77;stro\
ke-miterlimit:10\
;}\x0a\x09.st65{fill:#\
FF9191;stroke:#F\
F9191;stroke-mit\
erlimit:10;}\x0a\x09.s\
t66{fill:#FFFFFF\
;stroke:#FFFFFF;\
stroke-miterlimi\
t:10;}\x0a</style>\x0a\
<g id=\x22Layer_1\x22>\
\x0a\x09<path class=\x22s\
t0\x22 d=\x22M491.72,5\
6.23l-33.49-0.24\
c-4.66-0.03-9.46\
-1.75-13.43,0.7l\
-20.16,25c-5.14,\
3.18-20.77,18.14\
-38.17,29.44\x0a\x09\x09c\
-23.54,15.3-49.0\
5,28.06-44.37,34\
.77l12.46,8.32c1\
0.63,7.26,23.55,\
13.82,18.67,25.3\
8l-43.99,128.14\x0a\
\x09\x09c-1.67,3.96-9.\
93,26.87-10.31,3\
5.73c-0.4,9.17,2\
.18,13.34,6.35,2\
1.15c3.98,7.47,6\
.19,10.86,13.04,\
14.8\x0a\x09\x09c7.56,4.3\
5,8.79,4.44,13.1\
9,6.08l20.01,2.3\
7l51.83,4.3l4.73\
,95.15l61.86,0.7\
6L491.72,56.23z\x22\
/>\x0a\x09<path class=\
\x22st2\x22 d=\x22M363.93\
,283.89c0,0,12.0\
2,3.35,19.63,1.6\
3c7.53-1.7,30.12\
-12.29,30.12-12.\
29\x22/>\x0a\x09<g>\x0a\x09\x09<pa\
th class=\x22st4\x22 d\
=\x22M315.02,140.88\
l47.05,138.87c1.\
2,3.55-2.48,7.88\
-7.88,9.28l-248.\
12,64.11c-4.59,1\
.18-8.82-0.19-9.\
86-3.19\x0a\x09\x09\x09L61.6\
4,249.7c-1.04-3,\
1.45-6.69,5.79-8\
.58l235.64-102.7\
4C308.21,136.14,\
313.82,137.31,31\
5.02,140.88z\x22/>\x0a\
\x09\x09<path class=\x22s\
t5\x22 d=\x22M267.07,2\
25.17l25.37,8.05\
c3.88,1.23,7.62,\
2.83,11.18,4.79c\
2.54,1.4,5.19,2.\
6,7.96,3.47l10.4\
8,3.29\x0a\x09\x09\x09c7.96,\
2.5,24.61,5.89,3\
0.55,11.75l0.04-\
0.19c0.61,0.39,7\
.27,18.26,6.68,1\
8.68c-9.05,6.4-9\
4.81,18.97-103.1\
9,21.16l-125.5,3\
2.87\x0a\x09\x09\x09c-10.32,\
2.7-19.86-0.41-2\
2.09-7.22l-19.68\
-59.99c-1.75-5.3\
4,2.66-11.84,10.\
31-15.2l119.98-5\
2.76c6.56-2.88,1\
8.26,7.63,25.66,\
16.64\x0a\x09\x09\x09C250.57\
,217.53,258.38,2\
22.57,267.07,225\
.17z\x22/>\x0a\x09\x09\x0a\x09\x09\x09<e\
llipse transform\
=\x22matrix(0.9456 \
-0.3253 0.3253 0\
.9456 -70.7861 6\
4.2362)\x22 class=\x22\
st6\x22 cx=\x22156.69\x22\
 cy=\x22243.79\x22 rx=\
\x220.11\x22 ry=\x220.07\x22\
/>\x0a\x09\x09\x0a\x09\x09\x09<ellips\
e transform=\x22mat\
rix(0.9456 -0.32\
53 0.3253 0.9456\
 -70.7861 64.236\
2)\x22 class=\x22st6\x22 \
cx=\x22156.69\x22 cy=\x22\
243.79\x22 rx=\x220.11\
\x22 ry=\x220.07\x22/>\x0a\x09\x09\
\x0a\x09\x09\x09<ellipse tra\
nsform=\x22matrix(0\
.9456 -0.3253 0.\
3253 0.9456 -78.\
0017 61.1373)\x22 c\
lass=\x22st6\x22 cx=\x221\
43.82\x22 cy=\x22263.8\
2\x22 rx=\x220.11\x22 ry=\
\x220.07\x22/>\x0a\x09\x09\x0a\x09\x09\x09<\
ellipse transfor\
m=\x22matrix(0.9456\
 -0.3253 0.3253 \
0.9456 -76.4391 \
54.6793)\x22 class=\
\x22st6\x22 cx=\x22125.29\
\x22 cy=\x22255.92\x22 rx\
=\x220.11\x22 ry=\x220.07\
\x22/>\x0a\x09</g>\x0a\x09<path\
 class=\x22st0\x22 d=\x22\
M249.09,465.82l2\
.09-63.33c0.15-4\
.7,1.65-9.26,4.3\
1-13.14l15.53-22\
.65c3.3-4.82,5.1\
3-10.49,5.25-16.\
33\x0a\x09\x09l2.09-96.66\
c-0.9-2.15,0.53-\
17.62-4.19-15.77\
l-31.55,12.03c-1\
1.33,4.44-21.55,\
31.43-23.73,43.4\
l-0.2,4.27\x0a\x09\x09c-0\
.49,10.7-7.58,19\
.97-17.78,23.25l\
-63.63,20.44c-7,\
2.25-11.74,8.76-\
11.74,16.11l-0.8\
3,115.68c-0.04,5\
.67,4.54,10.29,1\
0.21,10.29\x0a\x09\x09h95\
.99C240.73,483.4\
,248.77,475.62,2\
49.09,465.82z\x22/>\
\x0a\x09<path class=\x22s\
t0\x22 d=\x22M214.61,1\
30.67l-1.81,1.73\
c-5.37,5.15-7.4,\
12.88-5.25,20l5.\
98,19.82l4.79,20\
.82\x0a\x09\x09c2.23,9.7,\
9.9,17.22,19.64,\
19.26l3.92,0.82c\
4.77,1,12.1-2.68\
,13.48-3.38l0,0c\
6.97-5.84,9.65-1\
5.35,6.78-23.98l\
-7.78-23.36\x0a\x09\x09l-\
7.19-24.63c-1.87\
-6.41-7.4-11.08-\
14.03-11.86l-3.2\
-0.38C224.31,124\
.87,218.69,126.7\
6,214.61,130.67z\
\x22/>\x0a\x09<path class\
=\x22st0\x22 d=\x22M174.6\
1,143.67l-1.81,1\
.73c-5.37,5.15-7\
.4,12.88-5.25,20\
l5.98,19.82l4.79\
,20.82\x0a\x09\x09c2.23,9\
.7,9.9,17.22,19.\
64,19.26l3.92,0.\
82c4.77,1,12.1-2\
.68,13.48-3.38l0\
,0c6.97-5.84,9.6\
5-15.35,6.78-23.\
98l-7.78-23.36\x0a\x09\
\x09l-7.19-24.63c-1\
.87-6.41-7.4-11.\
08-14.03-11.86l-\
3.2-0.38C184.31,\
137.87,178.69,13\
9.76,174.61,143.\
67z\x22/>\x0a\x09<path cl\
ass=\x22st0\x22 d=\x22M13\
3.61,155.17l-1.8\
1,1.73c-5.37,5.1\
5-7.4,12.88-5.25\
,20l5.98,19.82l4\
.79,20.82\x0a\x09\x09c2.2\
3,9.7,9.9,17.22,\
19.64,19.26l3.92\
,0.82c4.77,1,12.\
1-2.68,13.48-3.3\
8l0,0c6.97-5.84,\
9.65-15.35,6.78-\
23.98l-7.78-23.3\
6\x0a\x09\x09l-7.19-24.63\
c-1.87-6.41-7.4-\
11.08-14.03-11.8\
6l-3.2-0.38C143.\
31,149.37,137.69\
,151.26,133.61,1\
55.17z\x22/>\x0a\x09<path\
 class=\x22st0\x22 d=\x22\
M94.56,169.17l-1\
.81,1.73c-5.37,5\
.15-7.4,12.88-5.\
25,20l5.98,19.82\
l4.79,20.82c2.23\
,9.7,9.9,17.22,1\
9.64,19.26\x0a\x09\x09l3.\
92,0.82c4.77,1,1\
2.1-2.68,13.48-3\
.38l0,0c6.97-5.8\
4,9.65-15.35,6.7\
8-23.98l-7.78-23\
.36l-7.19-24.63\x0a\
\x09\x09c-1.87-6.41-7.\
4-11.08-14.03-11\
.86l-3.2-0.38C10\
4.26,163.37,98.6\
4,165.26,94.56,1\
69.17z\x22/>\x0a</g>\x0a<\
g id=\x22Layer_2\x22>\x0a\
</g>\x0a<g id=\x22Laye\
r_3\x22>\x0a</g>\x0a<g id\
=\x22Layer_5\x22>\x0a\x09<g \
id=\x22Layer_4\x22>\x0a\x09<\
/g>\x0a</g>\x0a<g id=\x22\
Layer_6\x22>\x0a</g>\x0a<\
g id=\x22Layer_7\x22>\x0a\
</g>\x0a</svg>\x0a\
\x00\x00\x01y\
<\
svg xmlns=\x22http:\
//www.w3.org/200\
0/svg\x22 width=\x2232\
\x22 height=\x2232\x22 vi\
ewBox=\x220 0 24 24\
\x22><!-- Icon from\
 Huge Icons by H\
ugeicons - undef\
ined --><g fill=\
\x22none\x22 stroke=\x22#\
ffffff\x22 stroke-l\
inecap=\x22round\x22 s\
troke-linejoin=\x22\
round\x22 stroke-wi\
dth=\x221.5\x22 color=\
\x22#ffffff\x22><circl\
e cx=\x2212\x22 cy=\x2212\
\x22 r=\x2210\x22/><path \
d=\x22M9.5 10.5C9.9\
92 9.994 11.3 8 \
12 8m2.5 2.5C14.\
008 9.994 12.7 8\
 12 8m0 0v8\x22/></\
g></svg>\
\x00\x00\x08g\
<\
svg xmlns=\x22http:\
//www.w3.org/200\
0/svg\x22 width=\x2232\
\x22 height=\x2232\x22 vi\
ewBox=\x220 0 48 48\
\x22><g fill=\x22#ffff\
ff\x22 fill-rule=\x22e\
venodd\x22 clip-rul\
e=\x22evenodd\x22><pat\
h d=\x22M9.614 16.6\
3c1.556-1.608 3.\
112-2.144 5.186-\
1.072c1.868.965 \
2.895 1.061 3.83\
8 1.071c.983-.01\
 2.052-.106 3.99\
8-1.071c2.16-1.0\
72 3.78-.536 5.4\
01 1.072c1.91 1.\
896 2.5 3.87 2.7\
01 5.361q.035.18\
.063.36a3.501 3.\
501 0 0 0-.912 6\
.306l-.079.203a3\
.5 3.5 0 1 0-3.5\
2 6.02q-.142.176\
-.277.331c-.835.\
869-1.785 1.426-\
2.815 1.256c-3.2\
4-.537-3.78-.537\
-4.32-.537h-.47c\
-.518 0-1.037 0-\
4.148.537c-2.49.\
428-4.49-3.753-5\
.482-5.896c-1.56\
-3.363-1.871-6.8\
-1.757-8.58c.193\
-1.492.76-3.465 \
2.593-5.36\x22/><pa\
th d=\x22M37.845 18\
.09a4.5 4.5 0 0 \
1 2.716 5.755q-.\
049.133-.127.243\
a4.5 4.5 0 0 1 .\
88 5.801a4.5 4.5\
 0 0 1-1.055 1.1\
66q.021.22.021.4\
45a4.5 4.5 0 0 1\
-.54 2.14a4.5 4.\
5 0 1 1-5.108 7.\
341a4.5 4.5 0 0 \
1-7.093-4.988a4.\
5 4.5 0 0 1 0-8.\
987a4.5 4.5 0 0 \
1 4.501-5.999q.0\
14-.101.05-.202a\
4.5 4.5 0 0 1 5.\
755-2.715m-1.983\
 21.307a2.5 2.5 \
0 1 0 2.578-4.15\
3a1 1 0 0 1-.1-.\
042c-.665.46-1.4\
6.746-2.318.792c\
.167.47.258.978.\
258 1.506c0 .678\
-.15 1.32-.418 1\
.897m.16-12.39a4\
.5 4.5 0 0 1 3.4\
9 1.977a2.5 2.5 \
0 0 0 .457-1.091\
a2.5 2.5 0 0 0-3\
.692-2.573a4.5 4\
.5 0 0 1-.255 1.\
686m-.283-3.648a\
4.5 4.5 0 0 1 2.\
943-.2a2.5 2.5 0\
 0 0-4.71-1.678l\
-.029.072a4.5 4.\
5 0 0 1 1.796 1.\
806M31.78 23a2.5\
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
78-3.798-6.358zm\
9.746 7.91c-.354\
-1.091-1.196-2.3\
32-2.458-3.428c-\
1.36-1.18-3.08-2\
.079-4.884-2.376\
c.483 1.462 1.47\
3 2.779 2.774 3.\
806c1.333 1.051 \
2.947 1.76 4.568\
 1.999\x22/><path d\
=\x22m37.968 9.144l\
.182 1.118c.455 \
2.803-.377 5.648\
-1.738 7.846c-1.\
338 2.162-3.334 \
3.92-5.415 4.258\
l-.987.16l-.16-.\
986c-.4-2.465.14\
2-5.11 1.364-7.3\
1s3.175-4.036 5.\
667-4.767zm-1.69\
4 2.71c-1.365.71\
2-2.507 1.9-3.31\
2 3.348c-.824 1.\
484-1.266 3.19-1\
.241 4.83c1.02-.\
525 2.11-1.555 2\
.99-2.977c.948-1\
.53 1.559-3.373 \
1.564-5.2\x22/></g>\
</svg>\
\x00\x00\x08=\
\x00\
\x00 @x\x9c\xedY\xdbn\xe3\xc8\x11}\x9e\xf9\x0a\
F\xfb\x14\x80l\xf7\xfd\x22\x8fw!\xc9\xf2f\x81\x09\
\x10 \x80_\x03\x0f\xcd\xb5\x84\xe1J\x86\xa4\xf1%F\
\xfe=\xa7\x9al\x89\xf4r\x15y6\x8f\x1e\x022\xbb\
\xba\xfat]NU\xb74\x9f~z\xfa\xad\xce\x1e\xaa\
\xcdv\xb9^]\x8c\x04\xe3\xa3\xacZ\x95\xeb\xdb\xe5\xea\
\xeeb\xf4m\xf7k\xe1G?\xfd\xf8\xf1\xd3_\x8a\x22\
\xfb\xb9ZU\x9b\x9b\xddz3\xce&\xb7\xeb/U\xfb\
\xf9K]\x7f\xdb\xee\xe2D&5\x93\x8c\xe7\xd9?\xaf\
\x7f\xce\xe6O\xf7\xeb\xcd.\xfbG\xfd\xed\xae\xf8e\x95\
\xb1(\xbcnv\x1ag\x96q\x9eM\xbf-\xeb\xdb\x8c\
\xff5\xcb\x8a\x02\x9bl\x1f\xee\xba\xa6\x88Q\x06\xe3V\
\xdb\x8b\xd1b\xb7\xbb\x1f\x9f\x9d=>>\xb2G\xc5\xd6\
\x9b\xbb3\xc99?\x83~\xab2~\xaa\x97\xab\xafC\
\x8a\x22\x84p\x16g\xa1z1\xe2\xf7O\xa3\xec\xb9\xfd\
\xfb\xb8\xbc\xdd-.F\xc6\xd3\xe8\xe3\x87lQ-\xef\
\x16;\x08\x8ca\x9e\x14\x1e\x96\xd5\xe3tM\xcb2\x9e\
A-\x8b3\xa3l\xbb{\xae\xab\x8bQ\xb5\xba\xf9R\
W\xc5\x97\x9b\xf2\xeb\xddf\xfdmu;^U\x8fY\
O\xf7<\x1a8\xde\xde\xdf\x94Xp\xbf\xa9\xb6\xd5\xe6\
\xa1\x1a\x91\xb3\x84\x91\xed\x9e\xef!\xdfUO\xbb\xb3r\
\xbb\x85\xfc\x03\xdb\xee\xf8\xcb\xaf\xcb\xba\x1e\xffp\xa5\xa7\
\x93\x89=Gp\xd7_\xabW\xc3\x22\x1a?6i\xf8\
\xdbrWm\xea%\xfe\x8c\x05?\xffO\xc4\x11/\xb7\
\xcb\xed}}\xf3<^\xadWU+\x94\xc3\xe0\x97\xd3\
0\xf7\x937\x80\xab>x\x03*\xc3d:\x97{P\
\x1e\xff\xbd\x01T\xb7\xc6\xcd-={\x9c\xde\xf0\x14\x1c\
\xd3\xe2\x049\x9b\xcf\xfd\x1e\xa77<\x05\xc7\xbe\x0c\xfa\
\xd5\x1b\x9e\x82\xe3Z\x9c\xa9\xa2g\x8f\xd3\x1b\x9e\x82\xe3\
\x87\xe3s\x19\xe8y\x03N\x18\xc6y\xb3=\x22Qu\
\xa6\xfd\x95\x9b'\xa9\xd8\xc3O\xcd\xc4$\xe9+\xe6\xb5\
R\x95t/gb*\x93T\x9fR\x02\x83\x16\xa5\xd4\
_]\xd9\xa9\x0f\x87\x95\xdd\xe1\xf0\xca6\xd9\x91\xcei\
\x99\x9f\xd0\xf3\x96\x88\xb8>\xf5ZiJ\xdc\x95\xa1'\
I\xc3\xc0\x8eo\xe6\xa8L9\xf0\xc6Lu\xca\x81L\
9\x98(\xa7\xacN\xd2\x94\x83\xf9t6\xd7)\xda2\
\xe5 hz\x0e\xa6t\x87'\x99\xa2_\x86K\x7fP\
\xd9\xf4c\xb2\xcfTwx\xd2\xaev\x9fr\xfa\x97\xa4\
\xae\x1f\x80\x04\xdf\x1b\x9e\x04\xefO\x07RG\x81R\xd5\
\xd9i\xb8\xect\x81\xde\xf0\xa4\xd6\x9b2\xdek\xda\xe3\
\x1f\x94\xb63\xff\x96\xc8\xa9D\x92\xde\xca\xef\x01J\xbc\
\x92\x13+\xdd\xc1\xa2\xde\xf0$ \xd5\x8fQ+\xdd\x9f\
\x0b\x97\xf4$\xa9\x19(\x1f%\xd5<\xcc\xfa;\xba\xa3\
;&\xf6\xcc\xa4\x9a\xec\xcbG\xb9\xbe4\xc1\xf7\x86\xc3\
x\xfe\x94\x95\xa7\x84\x22\xd1\xa5\xd7\x83\xbe\xc3C\x9d\xe8\
\xd2[\xf9\x1ahpe\xe2\x87\x0b3\xe7Rei\xf9\
\xb2\xc6}f\xb9{\x1es\xe6$:Dk'\xe88\
\x9b%%5\xcc\xd1\xfe=cpS\xdd\x817\xde\xcb\
\xf3Cu\xf3\xbdRj\x1e~6\xb3\xea\xea\xd0\xaf\xbb\
\xc3a\xf8C\xb7\x88\x1d\xaa\x95\xee\xf3-\xa4\x93\x89a\
\xda\xff\xc1.|j\xd4q'B\xc7\x89`\xb9?\x1f\
\xd8\xd4\xf0\xae\x92\x0e\xe7\x03&\x18qhn\x97\x9d\xca\
\xea\x0d\x87\xef@\xb2o|+My\x99*o\x5c\xf7\
\xe8\xef\x0c\x87\xf1\xbayqZ\xa4\xbc\x84\xb9\xf5\x93C\
7\xeb\x0d\x87\x81L7\xc1\xfc\x8f\xae\x8b\x83K\xf7\xc5\
\xda\xdc7\xf6\xc5\xd5\x1d\x0e\xafL\x09nO\xc9}*\
\xbb\xc3\xe1\x95\xbec\xaeu\xdc\xa6T\x0a3\x91\xe9`\
5\xa9X\xc3\x9cs\x93\x92gyo\xa9\xd7\x1d*_\
]usy\x18\x0e\xdfCE\x17\x08Eq\xfe\x9d\xa4\
\xb0\x89\x14G\x8f\xfa\xc1\x95j\xe8\xb22pC8\x9a\
{\xab\x87\xe9\x8c\xb6>uG\xbb\x98=\x5c\xec\x82\x08\
\xa2\xe3sg8\xbc\xf2\xd5\xfd\xe0\xb4\xb0\x7f:\x8b\xdf\
\xd0\xf0M\xed.[\xde^\x8c>\xdf<W\x9b\x7f\x09\
\xfa\xeavv\xf7J*\x07\xa5jPj\xe8K^O\
\xa2\xa3$*\xfeN\xdb\xc6\xb9\xfb\x9b\xdd\x22+\xeb\x9b\
-\xbe\x0b\xd3\x199\xca\xa0\xf0w\xe9<\xb3\xb9\x12\x8e\
\x05_r\xc6en\x98\xf5\xf8P>\x0fLY|\x04\
\x91[\xe6K\xc1\x99\x94\x85a\xce\xe7\xd2\xa0\xa7\x16B\
1\xafr%\x99\x10\xf4\x1e\xf4\xc7\x0f\x1fJ\x07Y\xc1\
\x99P\xa4\xe4s\xcf\xb4\xcf\x95% RQ%\xd6\xb8\
\x5cB\xae\x0a\xc1x \x05`zSK\xa6]!h\
\x13\x05;\x84.,\xde\x0a\xc5D\x80\x146\x14Xb\
\x0a\xa1\x994u!0)\x0a\x07X\xda3*\x04\xc0\
hS`W\xe5\xc8\xcaB9f\xc8\x14'\xeah\x9e\
\x80SN\x94\xc0\x11!WXJR\xabr\x01\x07\xe2\
k.\x05\x8c\xfb\xdc\x8d\xc8\xbfGg\x03\xa1\xd3M\xe8\
\x82g^\xe7\xdah\xa6\xe4\xb5\xe0\x80)y!%B\
\x93\x0b\x18+\x0a\xcd\x99\x0fy\xfcl\xde\x17\x8a\x0bf\
\xcbF\x8773\x8dn\xde\xd1}PF\xc2w\xf2\x8c\
\xe7Q\xb7\xe8\xe8tQ\x17E\x04\x9c\x09\x18+L\xae\
\x83AX\xf2\xd6.g\xc9\xe7\xae\x91\xc3\xde\xb4DP\
\x06\xa91\xefL\xe80\xa1\x17\x92\xf7\xe0\xfd\xbf\x83'\
|\xdb\x82\x02\xb8,s\xc5\x15\xd3\xaa\x09\x1e\xd8\x0a\x8a\
3\xabs\x07\xf3\xe1\x9d\xb1\xd8V\x9a\x12l\x96\x85f\
\xdaRap\xf8DGb.\x1d\xae\x90\xf4\xee\xa2#\
\x16\x7f)x\xa4#\x1d\xa2n4\xec HR1\x08\
\x9e\xd2\xb9 )\xca\x864}\xdc\xc7\x00\xd8HDP\
\xa8\xc2\x1b\xc6\x1d\x05\x90v\xf3\xa2\x90XW\x04\x8a\xa2\
\xa3\x90\x896\x18\x14-\xeb\x9b\xe0q\x8a\x85\xa6Y\x19\
\x03\x0d+\x0bdU\x03\xdfP\xaca/J\x98i\xc4\
\xce\x01<\x97\xccR\xc4\x1dqC\xe9\xf8\x0a\xab@\x11\
\xff\xb9\x17\x91\xa3\xc4{o\xdfon\xdf\xef\xb4\xfb\x13\
\xb43M\xec\x84\x15\xc8q.\xb5f\xaeV\x8c{2\
\xd7\x95\x08\x9d\xa4\xb4\xe6\xc83(\x10\x88\x85\xb0J:\
L[S\x0b\x8d\xc0\x98<\x90\xbf`\x1aH\xa6is\
\xf8gi\x85\xa6\xd8\x1b\x15\xf3\x08\xdf\xea\x82\x80\xf3\x08\
L\xeb%\x82\xa5\x8a\x88L\xa6\xfb\x22\x22S\xba\xccg\
a#\xed\xa5E\xd0g\xc2 q\x06\x83\xe8\xa50\x90\
I\xd09\x06\xa2kx\xeb\xe1\xa6*w\xf4\xab\xbeT\
D\xb0\xf8\xc3\xbe\xe0@\x05M\x0e~\xdb\xfd\x0f\xfd\x12\
\x9c\xc6T\xfa\x99_p\xc07@U]/\xef\xb7U\
g\x95\x03\x04!\x07\xa2\x06\xde\x09\xda\x0784\xca6\
$\xf7\x8c\xa3\x8e7\x10KT\x84\xfc_0\x0a\xe9i\
a$\x0f \xec1\x98\xe1~A\xfe\xbb\x80h\xd0\xf5\
\xa1\xf6\x91T\x12\xdf-K0\x8dXdAz0\x12\
\xb5\xe8\xa8\xb2t\xa4\xa0@\xe6@^d.\x16\x83\xa6\
|I\x8a\xad!F\xfbX\x16\xc8\x02-p2f\x8e\
\x80\xf3\x06\x98\x00rB&\xa1\xc9M\xec\x13\x84\x9c\xcb\
\xa6\xb6#t\x11\xa1g\xc2\xa2\x81P\x1ecq\x08\x13\
\xa8\x9a\x8c\xa1\xcbM\xcf\xf2ar\xbaT\xd8\x9e\x05\x99\
\x8b`\x1e\x0a/QF\xb8\x96\x09\x22%\xe3h0\xe4\
\x07}\xc4\xb7\x85\x08L\xeb\x92fy\x94F\xa5|\xaf\
t\x0d\x90\xe6\x1e&\x9a\x8e\xd7Y\x1b\xdf\x16ED\x98\
\xc9\x80F\x8b\x90\x05\x17g\x92\x05\xe8\x9c\x87\x81\x19\xb6\
:\xb5#4<\x89V!\xa9W ,\xcc N\x0e\
\xb4/\xa9\xa7\xe0=\xde\x15\xa9\x15(b7j\x83\xda\
\xabS5\xeey\xde\xa0\xea\x84\x83\x1f^GmLS\
\x02A\x06\xbc\xa1\x9d\x81\xb3\x94\x17\x02\xcd\x1b\xd0\xa8E\
\x98\x85h\x1a\xaa1To8\x10\x08\xb3\x88\xa0\xd4\xa7\
\xdcL\xaa@u(\xa4\xa6\x16IfjJ\xb5\xa4\xe6\
\xdb3\xbau\xaf^\xae\xba\xe4\x0d\xa3\xecI\x80\xf7\x01\
\xb5O\xd5%\x88\xb08\x80H.\x89\xc8\x94]\xc8\xe9\
]c\xd7c R\x06x\xd3\x80(\x9e\x10\xd0U\x08\
-\x228N\xbb\x1c\x83\xb0\x8a\xc9\x16\x01hA\xb6 \
pxoF@H\xd4P\xae4o\xabH\xd1\x81\x90\
kMg\xe0\xb5R\xd4CA2G5\x81\x0a\x0c\xd4\
\xa5x\xeci\xdc6\xef\x0b\xe1P6\xa2\x8c*\xbc\x99\
\x89\xaayG\xf5A\xa0\xaaUK8\xd2,\x0e\x1a]\
\xc8\xbf\x0943\xefgB#v0\x83\x0a\x04\xd5\x92\
\x8c\xf2\x94\xba\x9e\x89G\xcfA\x85\xe5(\xac\xf7sp\
\x7f\x0e\xf6\x22\xf2\x1e\xbb?\x19\xbb\xdf\xff\x1e\xe1\xf6\xbf\
i\xd0\xff\xbe\xff\xf8\xf1\xbf\xd1l\x84r\
\x00\x00\x09\x9f\
<\
svg xmlns=\x22http:\
//www.w3.org/200\
0/svg\x22 width=\x2232\
\x22 height=\x2232\x22 vi\
ewBox=\x220 0 48 48\
\x22><g fill=\x22#ffff\
ff\x22><path d=\x22M27\
.743 11.65c0 1.0\
5-1.666 1.9-3.72\
 1.9c-2.056 0-3.\
721-.85-3.721-1.\
9s1.665-1.9 3.72\
-1.9s3.72.85 3.7\
2 1.9\x22/><path fi\
ll-rule=\x22evenodd\
\x22 d=\x22M21.304 11.\
65c.012.037.088.\
221.542.453c.505\
.258 1.273.447 2\
.176.447s1.67-.1\
89 2.176-.447c.4\
54-.232.53-.416.\
542-.453c-.012-.\
036-.088-.22-.54\
2-.453c-.505-.25\
8-1.273-.447-2.1\
76-.447s-1.67.19\
-2.176.447c-.454\
.232-.53.417-.54\
2.453m-.367-2.23\
4c.84-.43 1.933-\
.666 3.085-.666s\
2.245.237 3.086.\
666c.787.402 1.6\
35 1.138 1.635 2\
.234s-.848 1.832\
-1.635 2.234c-.8\
41.43-1.934.666-\
3.086.666s-2.244\
-.236-3.085-.666\
c-.788-.402-1.63\
6-1.137-1.636-2.\
234s.848-1.832 1\
.636-2.234\x22 clip\
-rule=\x22evenodd\x22/\
><path fill-rule\
=\x22evenodd\x22 d=\x22M1\
5.269 7.838C13.0\
26 8.984 12 10.3\
86 12 11.65c0 1.\
265 1.026 2.667 \
3.269 3.812c2.18\
8 1.118 5.282 1.\
838 8.753 1.838s\
6.565-.72 8.753-\
1.838c2.243-1.14\
5 3.27-2.547 3.2\
7-3.812s-1.027-2\
.666-3.27-3.812C\
30.587 6.721 27.\
494 6 24.022 6c-\
3.471 0-6.564.72\
-8.753 1.838m-.9\
1-1.78C16.884 4.\
767 20.302 4 24.\
022 4s7.139.768 \
9.663 2.057c2.47\
 1.262 4.36 3.18\
5 4.36 5.593s-1.\
89 4.332-4.36 5.\
593c-2.525 1.29-\
5.942 2.057-9.66\
3 2.057s-7.138-.\
768-9.663-2.057C\
11.89 15.982 10 \
14.058 10 11.65s\
1.889-4.331 4.36\
-5.593\x22 clip-rul\
e=\x22evenodd\x22/><pa\
th fill-rule=\x22ev\
enodd\x22 d=\x22M12 36\
.351v-24.7h-2v24\
.7c0 2.408 1.889\
 4.331 4.36 5.59\
3c2.524 1.29 5.9\
42 2.057 9.662 2\
.057c2.546 0 4.9\
51-.36 7.024-1h-\
7.024v-1c-3.471 \
0-6.564-.72-8.75\
3-1.838C13.026 3\
9.018 12 37.616 \
12 36.35m20.846 \
3.775l.478.975l-\
.64 1.307q.52-.2\
18 1.001-.464c2.\
47-1.262 4.36-3.\
185 4.36-5.593v-\
24.7h-2v24.7c0 1\
.251-1.005 2.637\
-3.199 3.775\x22 cl\
ip-rule=\x22evenodd\
\x22/><path d=\x22M15.\
79 20.3a1 1 0 1 \
1-2 0a1 1 0 0 1 \
2 0m0 7.6a1 1 0 \
1 1-2 0a1 1 0 0 \
1 2 0m0 7.6a1 1 \
0 1 1-2 0a1 1 0 \
0 1 2 0m0-11.4a1\
 1 0 1 1-2 0a1 1\
 0 0 1 2 0m0 7.6\
a1 1 0 1 1-2 0a1\
 1 0 0 1 2 0\x22/><\
path fill-rule=\x22\
evenodd\x22 d=\x22M23.\
022 18.3a1 1 0 0\
 1 1-1h9.302a1 1\
 0 0 1 .898 1.44\
l-.715 1.46l.715\
 1.461a1 1 0 0 1\
 0 .88L33.507 24\
l.715 1.46a1 1 0\
 0 1 0 .88l-.715\
 1.46l.715 1.46a\
1 1 0 0 1 0 .88l\
-.715 1.46l.715 \
1.46a1 1 0 0 1 0\
 .88l-.715 1.46l\
.715 1.46a1 1 0 \
0 1 0 .88l-.715 \
1.46l.715 1.46a1\
 1 0 0 1 0 .88l-\
.93 1.9a1 1 0 0 \
1-.898.56h-8.372\
a1 1 0 0 1 0-2h7\
.748l.44-.9l-.71\
5-1.46a1 1 0 0 1\
 0-.88l.715-1.46\
l-.715-1.46a1 1 \
0 0 1 0-.88l.715\
-1.46l-.715-1.46\
a1 1 0 0 1 0-.88\
l.715-1.46l-.715\
-1.46a1 1 0 0 1 \
0-.88l.715-1.46l\
-.715-1.46a1 1 0\
 0 1 0-.88l.715-\
1.46l-.715-1.46a\
1 1 0 0 1 0-.88l\
.226-.46h-7.699a\
1 1 0 0 1-1-1\x22 c\
lip-rule=\x22evenod\
d\x22/></g></svg>\
\x00\x00\x01\x0d\
<\
svg xmlns=\x22http:\
//www.w3.org/200\
0/svg\x22 width=\x2232\
\x22 height=\x2232\x22 vi\
ewBox=\x220 0 24 24\
\x22><path fill=\x22no\
ne\x22 stroke=\x22#fff\
fff\x22 stroke-line\
cap=\x22round\x22 stro\
ke-linejoin=\x22rou\
nd\x22 stroke-width\
=\x221.5\x22 d=\x22M5 20v\
-1a7 7 0 0 1 7-7\
v0a7 7 0 0 1 7 7\
v1m-7-8a4 4 0 1 \
0 0-8a4 4 0 0 0 \
0 8\x22/></svg>\
\x00\x00\x01{\
<\
svg xmlns=\x22http:\
//www.w3.org/200\
0/svg\x22 width=\x2232\
\x22 height=\x2232\x22 vi\
ewBox=\x220 0 24 24\
\x22><!-- Icon from\
 Huge Icons by H\
ugeicons - undef\
ined --><g fill=\
\x22none\x22 stroke=\x22#\
ffffff\x22 stroke-l\
inecap=\x22round\x22 s\
troke-linejoin=\x22\
round\x22 stroke-wi\
dth=\x221.5\x22 color=\
\x22#ffffff\x22><circl\
e cx=\x2212\x22 cy=\x2212\
\x22 r=\x2210\x22/><path \
d=\x22M9.5 13.5c.49\
2.506 1.8 2.5 2.\
5 2.5m2.5-2.5c-.\
492.506-1.8 2.5-\
2.5 2.5m0 0V8\x22/>\
</g></svg>\
\x00\x00!\x99\
<\
?xml version=\x221.\
0\x22 encoding=\x22utf\
-8\x22?>\x0a<!-- Gener\
ator: Adobe Adob\
e Illustrator 24\
.2.0, SVG Export\
 Plug-In . SVG V\
ersion: 6.00 Bui\
ld 0)  -->\x0a<svg \
version=\x221.1\x22 xm\
lns=\x22http://www.\
w3.org/2000/svg\x22\
 xmlns:xlink=\x22ht\
tp://www.w3.org/\
1999/xlink\x22 x=\x220\
px\x22 y=\x220px\x22\x0a\x09 wi\
dth=\x22595.28px\x22 h\
eight=\x22555.8px\x22 \
viewBox=\x220 0 595\
.28 555.8\x22 style\
=\x22enable-backgro\
und:new 0 0 595.\
28 555.8;\x22\x0a\x09 xml\
:space=\x22preserve\
\x22>\x0a<style type=\x22\
text/css\x22>\x0a\x09.st0\
{fill:#F4BAA6;st\
roke:#F4BAA6;str\
oke-width:5;stro\
ke-miterlimit:10\
;}\x0a\x09.st1{display\
:none;}\x0a\x09.st2{fi\
ll:#F4BAA6;strok\
e:#DB9E8A;stroke\
-width:5;stroke-\
miterlimit:10;}\x0a\
\x09.st3{display:no\
ne;fill:#29ABE2;\
stroke:#000000;s\
troke-width:5;st\
roke-miterlimit:\
10;}\x0a\x09.st4{fill:\
#E6E6E6;stroke:#\
E6E6E6;stroke-wi\
dth:5;stroke-mit\
erlimit:10;}\x0a\x09.s\
t5{fill:#92CEE8;\
stroke:#92CEE8;s\
troke-width:5;st\
roke-miterlimit:\
10;}\x0a\x09.st6{fill:\
#29ABE2;stroke:#\
29ABE2;stroke-wi\
dth:5;stroke-mit\
erlimit:10;}\x0a\x09.s\
t7{fill:#B3B3B3;\
stroke:#B3B3B3;s\
troke-width:5;st\
roke-miterlimit:\
10;}\x0a\x09.st8{fill:\
#E6E6E6;stroke:#\
D9D9D9;stroke-wi\
dth:5;stroke-mit\
erlimit:10;}\x0a\x09.s\
t9{fill:#E6E6E6;\
stroke:#B3B3B3;s\
troke-width:5;st\
roke-miterlimit:\
10;}\x0a\x09.st10{fill\
:#C48F7E;}\x0a\x09.st1\
1{fill:#E6B5A5;}\
\x0a\x09.st12{fill:#F4\
BAA6;}\x0a\x09.st13{fi\
ll:#EDC1B2;}\x0a\x09.s\
t14{fill:#F4BAA6\
;stroke:#F4BAA6;\
stroke-miterlimi\
t:10;}\x0a\x09.st15{fi\
ll:#FF6B89;strok\
e:#FF6B89;stroke\
-miterlimit:10;}\
\x0a\x09.st16{fill:non\
e;stroke:#8A8A8A\
;stroke-width:5;\
stroke-miterlimi\
t:10;}\x0a\x09.st17{fi\
ll:#92CEE8;}\x0a\x09.s\
t18{fill:#F5F5F5\
;}\x0a\x09.st19{fill:n\
one;stroke:#92CE\
E8;stroke-width:\
5;stroke-miterli\
mit:10;}\x0a\x09.st20{\
fill:#855B4E;}\x0a\x09\
.st21{fill:#A373\
64;}\x0a\x09.st22{fill\
:#EBCE42;}\x0a\x09.st2\
3{fill:#949494;s\
troke:#949494;st\
roke-width:5;str\
oke-miterlimit:1\
0;}\x0a\x09.st24{strok\
e:#000000;stroke\
-miterlimit:10;}\
\x0a\x09.st25{fill:#F5\
F5F5;stroke:#F5F\
5F5;stroke-width\
:5;stroke-miterl\
imit:10;}\x0a\x09.st26\
{fill:#FFFFFF;}\x0a\
\x09.st27{fill:#A37\
364;stroke:#A373\
64;stroke-width:\
5;stroke-miterli\
mit:10;}\x0a\x09.st28{\
fill:#A37364;str\
oke:#A37364;stro\
ke-width:3;strok\
e-miterlimit:10;\
}\x0a\x09.st29{fill:#6\
B9DB3;stroke:#6B\
9DB3;stroke-widt\
h:5;stroke-miter\
limit:10;}\x0a\x09.st3\
0{fill:#DB9E8A;s\
troke:#346C85;st\
roke-width:5;str\
oke-miterlimit:1\
0;}\x0a\x09.st31{fill:\
#346C85;stroke:#\
346C85;stroke-wi\
dth:5;stroke-mit\
erlimit:10;}\x0a\x09.s\
t32{fill:#2A627A\
;stroke:#2A627A;\
stroke-width:5;s\
troke-miterlimit\
:10;}\x0a\x09.st33{fil\
l:#6B9DB3;}\x0a\x09.st\
34{fill:#EDEDED;\
}\x0a\x09.st35{fill:no\
ne;stroke:#323E9\
C;stroke-width:7\
;stroke-miterlim\
it:10;}\x0a\x09.st36{f\
ill:#C23A4E;}\x0a\x09.\
st37{fill:#C23A4\
E;stroke:#C23A4E\
;stroke-miterlim\
it:10;}\x0a\x09.st38{f\
ill:#C23A4E;stro\
ke:#C23A4E;strok\
e-width:5;stroke\
-miterlimit:10;}\
\x0a\x09.st39{fill:#8A\
8A8A;stroke:#323\
E9C;stroke-width\
:7;stroke-miterl\
imit:10;}\x0a\x09.st40\
{fill:#323E9C;st\
roke:#323E9C;str\
oke-miterlimit:1\
0;}\x0a\x09.st41{fill:\
#79C77F;}\x0a\x09.st42\
{opacity:0.7294;\
fill:#8DB9CC;}\x0a\x09\
.st43{fill:#DB9E\
8A;stroke:#DB9E8\
A;stroke-miterli\
mit:10;}\x0a\x09.st44{\
opacity:0.5882;f\
ill:#FFFF00;}\x0a\x09.\
st45{fill:#8CC63\
F;stroke:#8CC63F\
;stroke-miterlim\
it:10;}\x0a\x09.st46{f\
ill:#FF0000;}\x0a\x09.\
st47{fill:#C1272\
D;}\x0a\x09.st48{fill:\
#8CC63F;stroke:#\
80B53A;stroke-mi\
terlimit:10;}\x0a\x09.\
st49{opacity:0.9\
608;fill:#FF0000\
;}\x0a\x09.st50{opacit\
y:0.949;fill:#C1\
272D;}\x0a\x09.st51{fi\
ll:#FFFD7A;strok\
e:#FFFD7A;stroke\
-miterlimit:10;}\
\x0a\x09.st52{fill:#8C\
C63F;}\x0a\x09.st53{fi\
ll:#B38576;strok\
e:#B38576;stroke\
-miterlimit:10;}\
\x0a\x09.st54{opacity:\
0.7412;fill:#9E6\
8A3;stroke:#9E68\
A3;stroke-miterl\
imit:10;}\x0a\x09.st55\
{opacity:0.502;s\
troke:#000000;st\
roke-miterlimit:\
10;}\x0a\x09.st56{fill\
:#C48F7E;stroke:\
#C48F7E;stroke-m\
iterlimit:10;}\x0a\x09\
.st57{fill:#855B\
4E;stroke:#855B4\
E;stroke-miterli\
mit:10;}\x0a\x09.st58{\
opacity:0.6706;f\
ill:#F15A24;}\x0a\x09.\
st59{fill:#9E005\
D;}\x0a\x09.st60{opaci\
ty:0.6784;fill:#\
FFFFFF;stroke:#F\
FFFFF;stroke-mit\
erlimit:10;}\x0a\x09.s\
t61{opacity:0.65\
88;fill:#FFFD7A;\
stroke:#FFFD7A;s\
troke-miterlimit\
:10;}\x0a\x09.st62{fil\
l:#949494;stroke\
:#949494;stroke-\
miterlimit:10;}\x0a\
\x09.st63{fill:none\
;stroke:#949494;\
stroke-width:3;s\
troke-miterlimit\
:10;}\x0a\x09.st64{fil\
l:#FFFD7A;stroke\
:#EDEB77;stroke-\
miterlimit:10;}\x0a\
\x09.st65{fill:#FF9\
191;stroke:#FF91\
91;stroke-miterl\
imit:10;}\x0a\x09.st66\
{fill:#FFFFFF;st\
roke:#FFFFFF;str\
oke-miterlimit:1\
0;}\x0a</style>\x0a<g \
id=\x22Layer_1\x22>\x0a</\
g>\x0a<g id=\x22Layer_\
2\x22>\x0a</g>\x0a<g id=\x22\
Layer_3\x22>\x0a</g>\x0a<\
g id=\x22Layer_5\x22>\x0a\
\x09<g id=\x22Layer_4\x22\
>\x0a\x09</g>\x0a</g>\x0a<g \
id=\x22Layer_6\x22>\x0a\x09<\
path class=\x22st43\
\x22 d=\x22M345.76,309\
.87c-0.02-0.01-0\
.02-0.05,0-0.06l\
5.7-4.54c3.71-2.\
85,5.84-7.32,5.7\
3-12.03l0.05-12.\
02l3.95,4.82\x0a\x09\x09c\
22.26,13.61,47.0\
5,11.61,68.42-3.\
38l5.68-3.25l-0.\
98,6.87c-0.6,7.5\
7,1.9,15.06,6.91\
,20.72l2.61,1.77\
\x0a\x09\x09c0.09,0.06,0.\
09,0.18,0.01,0.2\
5l-41.7,31.49c-3\
.47,2.69-8.26,2.\
81-11.86,0.3L345\
.76,309.87z\x22/>\x0a\x09\
<path class=\x22st1\
4\x22 d=\x22M116.07,21\
0.24c0-13.92,8.4\
4-24.08,21.58-24\
.08c7.01,0,3.98,\
3.5,2.49,8.9c-1.\
3,4.73-0.69,10.9\
2-0.69,17.42\x0a\x09\x09c\
0,6.88,0.72,11.8\
6,3.79,17.11c3.1\
4,5.38,8.55,10.9\
6,1.9,10.96C132,\
240.55,116.07,22\
4.16,116.07,210.\
24z\x22/>\x0a\x09<ellipse\
 class=\x22st14\x22 cx\
=\x22208.95\x22 cy=\x2220\
4.59\x22 rx=\x2269.17\x22\
 ry=\x2293.02\x22/>\x0a\x09<\
path class=\x22st14\
\x22 d=\x22M302.09,210\
.24c0-13.92-9.56\
-24.08-24.45-24.\
08c-7.94,0-4.5,3\
.5-2.82,8.9c1.47\
,4.73,0.78,10.92\
,0.78,17.42\x0a\x09\x09c0\
,6.88-0.82,11.86\
-4.29,17.11c-3.5\
6,5.38-9.69,10.9\
6-2.15,10.96C284\
.05,240.55,302.0\
9,224.16,302.09,\
210.24z\x22/>\x0a\x09<pat\
h class=\x22st51\x22 d\
=\x22M82.21,467.59l\
203.44,2.01l2.01\
-106.99c0.87-11.\
76,7.43-22.33,17\
.54-28.24l22.93-\
5.7l16.72-18.27l\
-82.3-0.19\x0a\x09\x09c-2\
.34-0.01-4.63,0.\
66-6.61,1.93l-7.\
13,4.57c-22.81,1\
5.23-52.34,14.25\
-72.85-4.01l-9.2\
3-6.37c-4.33-0.0\
8-3.66,2.39-7.85\
,3.48\x0a\x09\x09l-39.3,1\
0.29c-25.14,11.9\
3-37.6,30.97-39.\
81,58.93L82.21,4\
67.59z\x22/>\x0a\x09<path\
 class=\x22st14\x22 d=\
\x22M166.26,305.44L\
166.26,305.44c4.\
92-5.54,6.64-13.\
27,4.53-20.4l-1.\
08-3.66l10.88,6.\
95\x0a\x09\x09c19.99,12.7\
7,44.87,11.95,62\
.71-4.37l3.57-4.\
33l-0.41,3.15c-1\
.34,10.25,2.6,20\
.49,10.45,27.14l\
0.65,0.55l-11.83\
,7.15\x0a\x09\x09c-20.69,\
14.54-47.09,13.6\
6-66.98-2.22L166\
.26,305.44z\x22/>\x0a\x09\
<path class=\x22st5\
3\x22 d=\x22M139.78,18\
4.64c0-34.56,35.\
55-73.18,69.17-7\
3.18s69.17,39.19\
,69.17,73.74c0,6\
.48,1.99,27.06-0\
.23,27.01\x0a\x09\x09c-3.\
23-0.09-19.11,3.\
26-25.97-8.49c-2\
.33-4-4.28-10.12\
-7.46-12.13c-3.1\
8-2.01-7.6,0.08-\
10.45-5.36\x0a\x09\x09c-2\
.34-4.45-0.21-16\
.17-2.49-21.29c-\
2.09-4.68-11.74,\
0.47-14.14,1.29c\
-7.26,2.48-9.17,\
1.65-16.17,1.65c\
-5.1,0-7.79-2.94\
-15.68-6.08\x0a\x09\x09c-\
1.44-0.57-3.91-0\
.49-4.74,2.12c-2\
.07,6.55,1.87,9.\
41-1.3,15.93c-2.\
74,5.64-6.49-1.8\
7-9.09,3.84\x0a\x09\x09c-\
7.38,16.24-25.54\
,37.62-29.13,40.\
17C138.4,225.91,\
139.78,193.28,13\
9.78,184.64z\x22/>\x0a\
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
-1.62-3.6-3.6s1.\
62-3.6 3.6-3.6s3\
.6 1.62 3.6 3.6s\
-1.62 3.6-3.6 3.\
6\x22/></svg>\
\x00\x00\x03Z\
<\
svg xmlns=\x22http:\
//www.w3.org/200\
0/svg\x22 viewBox=\x22\
0 0 415.44 413.0\
8\x22><defs><style>\
.cls-1{fill:#122\
74b;}.cls-2{fill\
:#2a7abf;}.cls-3\
{fill:#1468b1;}<\
/style></defs><g\
 id=\x22Capa_2\x22 dat\
a-name=\x22Capa 2\x22>\
<g id=\x22Capa_1-2\x22\
 data-name=\x22Capa\
 1\x22><path class=\
\x22cls-1\x22 d=\x22M106.\
54,125.2C182.6-8\
4.53,321.71-36.4\
9,366.37,312.76c\
1.11,8.71-5.64,1\
6.19-13.88,15.57\
-23-1.73-55.55-1\
5.19-93.64-35.57\
a13.92,13.92,0,0\
,1-7.14-12.62C25\
6.3,61.87,226-46\
.65,106.54,125.2\
Z\x22/><path class=\
\x22cls-2\x22 d=\x22M166.\
58,402c-208.32,3\
9.09-241.43-112.\
29,17-333.25,6.4\
4-5.51,16-3.23,1\
9.72,4.59,10.5,2\
1.85,16.43,58.38\
,19.67,103.56a14\
,14,0,0,1-6.48,1\
3C38.21,298.42-3\
3.62,382,166.58,\
402Z\x22/><path cla\
ss=\x22cls-3\x22 d=\x22M3\
59.47,207C492.66\
,381.62,384.11,4\
85.79,76.89,352.\
77c-7.66-3.31-10\
.4-13.25-5.78-20\
.54,12.89-20.35,\
40.08-43.58,75.7\
-68.5a12.32,12.3\
2,0,0,1,13.86-.2\
8C336.47,376.51,\
440.12,402.7,359\
.47,207Z\x22/></g><\
/g></svg>\
\x00\x00\x06\x91\
\x00\
\x00\x17tx\x9c\xc5X[o\xdb6\x14~n\x7f\x05\
\xa7\xbe\xac\x80D\xf3~q\x9a\x0e\xb6\xe3\xb4\x05:`\
@\x81\xbe\x0e\xae\xa3&F]\xdb\x90\x15'i\xb0\xff\
\xbeCJ\x94\xa8\x94M\x9d>l\x11 \xeb\x1c\x1e~\
\xfcxn\xa2\xf2\xea\x8f\xdb\xafkt(\xab\xfdj\xbb\
9\xcd(&\x19*7\xcb\xed\xc5jsy\x9a]\xd7\
\x9f\x0b\x93\xfd\xf1\xfa\xf9\xab\xdf\x8a\x02\xbd)7e\xb5\
\xa8\xb7\xd5\x18M.\xb6\x9f\xca\xf6\xfen\xbd\xbe\xde\xd7\
~\x001\x81\x19&9\xfa\xf0\xf1\x0d\x9a\xdf\xee\xb6U\
\x8d\xfeZ__\x16\xef6\x08{\xe5\xc7f\xa51R\
\x98\x104\xbd^\xad/\x10y\x89PQ\xc0\x22\xfb\xc3\
eL\x85f\x08\xc8m\xf6\xa7\xd9U]\xef\xc6\xa3\xd1\
\xcd\xcd\x0d\xbe\xe1x[]\x8e\x18!d\x04\xf6\xad\xc9\
\xf8v\xbd\xda|I\x19Rk\xed\xc8\x8f\x82\xe9iF\
v\xb7\x19\xbak~\x9f?C7\xab\x8b\xfa\xea4\x93\
Vbf\xdc\xd0U\xb9\xba\xbc\xaaA#\xbd\xe5aU\
\xdeL\xb7n\x1e\x22\xa8\xb1B0\x94\xa1}}\xb7.\
O\xb3r\xb3\xf8\xb4.\x8bO\x8b\xe5\x97\xcbj{\xbd\
\xb9\x18o\xca\x1b44>\xf1\x1c\xc7\xfb\xddb\x093\
vU\xb9/\xabC\x99\xb9\xfd:\x10T\xdf\xed@_\
\x97\xb7\xf5h\xb9\xdf\x83\xfe\x19\xde\xd7\xe4\xfe\xf3j\xbd\
\x1e\xbf8\x17\xd3\xc9D\x9d\x80\x7f\xb7_\xca\x07b\xe1\
\xd9\x8fe\x10\xbf\xae\xea\xb2Z\xaf\xe0gL\xc9\xc9?\
\x1e\x87\xde_\xac\xf6\xbb\xf5\xe2n\xbc\xd9n\xcaV\xc9\
\xd2\xe0gS;7\x93'\x80\xf3!x\x03\xca\xecd\
:g\x1d(\xf1\x7fO\x00\x15-\xb9\xb9rW\x873\
\x10\x8f\xc1\x91-\x8ee\xb3\xf9\xdct8\x03\xf1\x18\x1c\
u\x9f\xdc\xd7@<\x06G\xb78S\xee\xae\x0eg \
\x1e\x83c\xd2\xfe9\xb3\xeez\x02\x8eM\xe3<\x99\x0f\
\x0d\xa9:\x13\xe6\x5c\xcf\x83\x96v\xf0S9\x91A\xfb\
 \xf3Z-\x0f\xb6g3:eA+\x8e)\x81$\
\xa3\x10\xfa\xf3s55\xb6\x9f\x19\x8b\xe9\x99m\xb0}\
:\x87if\xe2\xae\xa7xD\x0fS\xaf\xd5\x86\xc0\x9d\
Kw\x05\xadM\xac\xf8\xe4\x1ce!\x06F\xca\xa9\x08\
1`!\x06\x13\xae\xb9\x12A\x1bb0\x9f\xce\xe6\x22\
x\x9b\x85\x18X\xe1\xae\x9eJ,\x1eEE\xdc\xa7K\
?i,\x87>\xe9\x22\x15\x8bG\xad\xaa\xba\x90\xbb\xbf\
\xa0\xd5C\x07\x04\xf8\x81x\x14\xbc9\x1e\x88?\x0a\x14\
\xaaNM\xedY\xd4\x05\x06\xe2Q\xad7D|\xd0\xb4\
\xc7/\xb8P3\xf3\x14\xcf\xf1\x90$\x83\x99\xbf\x02\x14\
\xf2\x8aM\x14\xd3=\xa3\x81x\x14\x10\x1f\xfa\xa8\xd5v\
\xef\x853w\x05\xadL\x94\x0fg|ng\xc3\x15\xf5\
\xa3+\x86\xec\x991>\xe9\xca\x87\xeb\xa16\xc0\x0f\xc4\
4\x9e9f\xe61\xae\x08\xe92\xe8A\xbf\xb0C\x11\
\xd2e0\xf3!Prf\xc8\x0fmgZ\x87\xca\x12\
\xec~\x0b\xe7\x99U}7&X3\xe8\x10-OH\
\xc7\xd9,\x18\xf1t\x8e\x0e\xcf\x19\xc9EE\x04/\x8d\
a'}u\x93\xce(4\x0f3\x9b)~\xde\xf7\xeb\
XL\xc3\xf7\xdd\xc2w\xa8V\xdb\xc5\x9b2\xcdB\x86\
\x09\xf3\x83U\xc8T\xf2\xc77a\xa3MXE\xccI\
bQIb#aO\x12\x14$\xed\x9b\xdbYTY\
\x031}\x06bC\xf2\xad6\xc4e\xca\x8d\xd4\xf1\xab\
?\x12\xd3xq\x5c\xb4\xa0!.v\xae\xcc\xa4\xeff\
\x031\x0d$\xe3\x00\x93\x1f\x1d\x17\x93S\xbbbm\xce\
\x1b]q\xc5bzf\x08p\xfb\x96\xecB\x19\x8b\xe9\
\x99&\xa2\xab4Q!\x94TNXx\xb1\xcaP\xac\
vN\x88\x0c\xc1Sd0\xd5\x88(\x95\xcf\xcf\xe3X\
\xf6b\xfa\x1cJc (\x8a\x93_L\x0a\x15\x92\xe2\
\xd1W}r&O\x1dV\x12'\x84Gc\xafD:\
\x9d\xa1\xadO\xf5\xa3]L\xf5\x07;K-\x8d\xf6\x1c\
\x89\xe9\x99\x0f\xce\x07\xc7\xb9\xfd\xd5\xc8\x7f\xa1\xc1\x97\xda\
%Z]\x9cf\xef\x17we\xf57u\x9fn\xa3\xcb\
\x07Z\x96\xd4r\xf79\xf7j\xb7\xa8\xaf\xd0r\xbd\xd8\
\xc3\xa7\xac;0g\x08\x0c\xfe\xb4\x0aS\x96s\xc2\xb1\
\x96\xefcaI\x0a\x83\xa5\xca\x154\x84\x82J,s\
w\xf3OW\x8c\x91\xa5\x1f$^\xe9m\xf2\xce\xe6@\
\x9e?{\xb6$\xb9\xb3(\xba\xa1\x1e\xe3\xaa\x80\xf93\
\x0a\xab\x10\x95sj1\x93y\xbb2e\x98\xd3<\xa6\
\xf1-\x1b9\xf2U\xb9\xac\xdd\x973\xa5\x1aZ\xb1\xff\
x\xa6\xc6b\x9b\xf5;b\xb0\xa3\xf6K\x9a\x9a\xfe\x1b\
\x9aj\x82\xb9\x1e\xa2p\x221W\x0d\x8a\x15\x98\xf24\
\x0cc1\x8cm0\x86nd\xb4q\xa3\xb6X\xd3\x9c\
Y\x8e\x0d=\x14\xb0\x0d\xa1\xc0\x81\x1c~r\x06*p\
\x03\xd3\xb9\xbb\xf9\xa7+\xe8\xab\xce\xc2\x8f\x13\xaf\xf7f\
ygv\xf0\x10\x8d\x1f\x9dU\xd1\x0d\xf7Po\x8d\xc4\
\xd6\xcc\x0c\xc3\x92\x82\xb7\x08&&\x0f<\xb43\x8aI\
};\x82=\xb7\xff\x17{&T\xc4^\xf0\x88\xbd'\
\xf53\xf6\x90.\x8cP\xac\xd5\x7f\xc9\x9e\xdb\x99\xa1\xd8\
rX\xda`\xc2\xf3\xc0Cb\xd6\x0b\x8eT\xcb~\xb9\
\xaa\x96\xeb2\xe2\x0f\xe9\xb5\xf49\xad`\xa7\xf0\xec\xd2\
\x91h\xccE\x86*HR\xf0\x8c\x9b\xf8}=K_\
\xcf\xb1Fx\x8d7\xfc\xceZeq\xea\x0b\x09y\xd2\
\xa4>\xd3\xc6W\xc1\xa0'\x84\xd4\xe7}\xea\x1b\xd3\x10\
y\xe8\x7f\xd1\xfa_0li. P\xdc\x1e\x0a\x03\
Uk\xc0\xff\xe0\x19\x9bS\xac\x18DBA~\xc2\xcd\
?\xbd\x95\xcep\xe9\x87\x89W{\xab\xbc\xb3:x\x84\
\xc6\xfd\xce\xaa\xe8\x86{\xa4\xb7\x90/\x92\xcd\x84\x80{\
.\x04\xcf[\x0e\x82bn\xf2\x98P\xeb\xfbr\xbd^\
\xed\xf6\xe5\x90\xbcs\xbe\x22M\xf9\xdf9\x87Kh8\
\xe0{PC\x03\xa9\x9c\x8b\xba\xad\x07\x80\xbaZl\xf6\
\x9f\xb7\xd5\xd7\xd3\xec\xeb\xa2\xaeV\xb7\xbf\xbbc\x15*\
\x88\xfb?[{s\xb2e\xc0Z\x22\x00\x80C\x94}\
\x99}\xbf\xb2d\xfd\xca\xdc`\xe7q\xb72d\x97\xfc\
\xd1\xe2\xdfap\xe8\x81=}h\x8d\x03\xf6\xe0\x07\xdd\
 \x807\x1f\xdd\x01\xd3\x92\xbb=XE9\xea~\x1a\
\xad\xf3\xa9\xb5\x12)\x06\x9d\x9ap\x9d\xda\x0b\x87\x96\xad\
d\xcb\x03\x96u\x19\xe6\x884\x0c<\x19\xf3\x93\xadH\
\xa0Oe\xef\x8f_\xde\x8a\xa5\xdaoE*\x89\xba\x1f\
\xafU\xb0\x13.\x05\xd2\xe0z!%MF\x05\x96\xd6\
\x22\xd0\x10P\xf9\x0d\x0f\x06\x85\xcc\x1b.\xf2\xf1rh\
|\x913J\x9bB\x90\xb0/\x91\xbb`\xc2{\x94s\
pn\xae\xa0\xe0M+\xec\x15\xa4;\xcb\xb5\xc2\x9c\xe5\
\xcd\xb3\x1b\x10j_@>Z\xedF,\xbcG\x05f\
\xacy\x06\x0f|\x08\x8b(\x83-\x14G\xbc\xe4\xb7t\
\xd3\xd0\xdd\xd1\xc0\xfd\xc7\xfa\xf5\xf3\x7f\x01\xd9~\xce\x92\
\
\x00\x00\x01^\
<\
svg xmlns=\x22http:\
//www.w3.org/200\
0/svg\x22 width=\x2232\
\x22 height=\x2232\x22 vi\
ewBox=\x220 0 24 24\
\x22><path fill=\x22no\
ne\x22 stroke=\x22#fff\
fff\x22 stroke-line\
cap=\x22round\x22 stro\
ke-linejoin=\x22rou\
nd\x22 stroke-width\
=\x221.5\x22 d=\x22M9.172\
 14.828L12.001 1\
2m2.828-2.828L12\
.001 12m0 0L9.17\
2 9.172M12.001 1\
2l2.828 2.828M12\
 22c5.523 0 10-4\
.477 10-10S17.52\
3 2 12 2S2 6.477\
 2 12s4.477 10 1\
0 10\x22/></svg>\
"

qt_resource_name = b"\
\x00\x06\
\x06\xfaec\
\x00i\
\x00c\x00o\x00n\x00o\x00s\
\x00\x0b\
\x0aGg\x04\
\x00i\
\x00c\x00o\x00n\x00s\x00s\x00e\x00l\x00e\x00c\x00t\
\x00\x1a\
\x00\xbc\x1d\x87\
\x00I\
\x00c\x00B\x00a\x00s\x00e\x00l\x00i\x00n\x00e\x00Q\x00u\x00e\x00s\x00t\x00i\x00o\
\x00n\x00M\x00a\x00r\x00k\x00.\x00s\x00v\x00g\
\x00\x11\
\x05\xaa\xf4\x87\
\x00I\
\x00c\x00o\x00n\x00o\x00i\x00r\x00S\x00e\x00a\x00r\x00c\x00h\x00.\x00s\x00v\x00g\
\
\x00\x1e\
\x08\xf9\xe0g\
\x00H\
\x00u\x00g\x00e\x00i\x00c\x00o\x00n\x00s\x00C\x00i\x00r\x00c\x00l\x00e\x00A\x00r\
\x00r\x00o\x00w\x00L\x00e\x00f\x00t\x000\x002\x00.\x00s\x00v\x00g\
\x00\x1d\
\x0e\xb8\x9a\xe7\
\x00I\
\x00c\x00S\x00h\x00a\x00r\x00p\x00M\x00o\x00t\x00i\x00o\x00n\x00P\x00h\x00o\x00t\
\x00o\x00s\x00P\x00a\x00u\x00s\x00e\x00d\x00.\x00s\x00v\x00g\
\x00\x1e\
\x0a\x04\xa2\xe7\
\x00H\
\x00e\x00a\x00l\x00t\x00h\x00i\x00c\x00o\x00n\x00s\x00H\x00e\x00a\x00r\x00t\x00C\
\x00a\x00r\x00d\x00i\x00o\x00g\x00r\x00a\x00m\x00.\x00s\x00v\x00g\
\x00\x1d\
\x0b!\xc3g\
\x00H\
\x00u\x00g\x00e\x00i\x00c\x00o\x00n\x00s\x00G\x00a\x00m\x00e\x00C\x00o\x00n\x00t\
\x00r\x00o\x00l\x00l\x00e\x00r\x000\x003\x00.\x00s\x00v\x00g\
\x00\x16\
\x03\xed\x82\x07\
\x00A\
\x00s\x00i\x00s\x00t\x00e\x00n\x00c\x00i\x00a\x00 \x00m\x00e\x03\x01\x00d\x00i\x00c\
\x00a\x00.\x00s\x00v\x00g\
\x00\x0a\
\x0f\xad\x16\xa7\
\x00C\
\x00o\x00m\x00i\x00d\x00a\x00.\x00s\x00v\x00g\
\x00\x17\
\x04\xe2\xba\x87\
\x00I\
\x00c\x00B\x00a\x00s\x00e\x00l\x00i\x00n\x00e\x00E\x00x\x00i\x00t\x00T\x00o\x00A\
\x00p\x00p\x00.\x00s\x00v\x00g\
\x00\x09\
\x0e\xa2\xcb\x87\
\x00B\
\x00a\x00n\x03\x03\x00o\x00.\x00s\x00v\x00g\
\x00\x0f\
\x08\x82iG\
\x00I\
\x00c\x00o\x00n\x00o\x00i\x00r\x00B\x00e\x00l\x00l\x00.\x00s\x00v\x00g\
\x00\x0e\
\x04sD\xc7\
\x00W\
\x00i\x00R\x00a\x00i\x00n\x00d\x00r\x00o\x00p\x00.\x00s\x00v\x00g\
\x00\x17\
\x09\x81\x87\x87\
\x00H\
\x00u\x00g\x00e\x00i\x00c\x00o\x00n\x00s\x00W\x00h\x00e\x00e\x00l\x00c\x00h\x00a\
\x00i\x00r\x00.\x00s\x00v\x00g\
\x00\x18\
\x05(V\xa7\
\x00P\
\x00e\x00p\x00i\x00c\x00o\x00n\x00s\x00P\x00e\x00n\x00c\x00i\x00l\x00P\x00e\x00o\
\x00p\x00l\x00e\x00.\x00s\x00v\x00g\
\x00\x1f\
\x0bjp\xc7\
\x00H\
\x00u\x00g\x00e\x00i\x00c\x00o\x00n\x00s\x00C\x00i\x00r\x00c\x00l\x00e\x00A\x00r\
\x00r\x00o\x00w\x00R\x00i\x00g\x00h\x00t\x000\x002\x00.\x00s\x00v\x00g\
\x00\x0a\
\x04\x0c7\xe7\
\x00D\
\x00o\x00r\x00m\x00i\x00r\x00.\x00s\x00v\x00g\
\x00\x13\
\x0f\xd0\xe0'\
\x00I\
\x00c\x00o\x00n\x00o\x00i\x00r\x00T\x00r\x00i\x00a\x00n\x00g\x00l\x00e\x00.\x00s\
\x00v\x00g\
\x00\x18\
\x0a\xcaRg\
\x00I\
\x00c\x00o\x00n\x00o\x00i\x00r\x00A\x00r\x00r\x00o\x00w\x00D\x00o\x00w\x00n\x00L\
\x00e\x00f\x00t\x00.\x00s\x00v\x00g\
\x00\x11\
\x0dt]G\
\x00I\
\x00c\x00o\x00n\x00o\x00i\x00r\x00E\x00x\x00p\x00a\x00n\x00d\x00.\x00s\x00v\x00g\
\
\x00\x0f\
\x08\xfdj'\
\x00I\
\x00c\x00o\x00n\x00o\x00i\x00r\x00M\x00e\x00n\x00u\x00.\x00s\x00v\x00g\
\x00\x08\
\x0e\xb4R'\
\x00A\
\x00g\x00u\x00a\x00.\x00s\x00v\x00g\
\x00\x1c\
\x05\xba\x9f\xa7\
\x00H\
\x00u\x00g\x00e\x00i\x00c\x00o\x00n\x00s\x00C\x00i\x00r\x00c\x00l\x00e\x00A\x00r\
\x00r\x00o\x00w\x00U\x00p\x000\x002\x00.\x00s\x00v\x00g\
\x00\x15\
\x0c\xf4%\x87\
\x00H\
\x00e\x00a\x00l\x00t\x00h\x00i\x00c\x00o\x00n\x00s\x00F\x00r\x00u\x00i\x00t\x00s\
\x00.\x00s\x00v\x00g\
\x00\x13\
\x0cH\x15\x07\
\x00E\
\x00n\x00t\x00r\x00e\x00t\x00e\x00n\x00i\x00m\x00i\x00e\x00n\x00t\x00o\x00.\x00s\
\x00v\x00g\
\x00\x1a\
\x0b\x17c'\
\x00H\
\x00e\x00a\x00l\x00t\x00h\x00i\x00c\x00o\x00n\x00s\x00T\x00o\x00i\x00l\x00e\x00t\
\x00P\x00a\x00p\x00e\x00r\x00.\x00s\x00v\x00g\
\x00\x0f\
\x05hk\xc7\
\x00I\
\x00c\x00o\x00n\x00o\x00i\x00r\x00U\x00s\x00e\x00r\x00.\x00s\x00v\x00g\
\x00\x1e\
\x0e\xfe\xda\x07\
\x00H\
\x00u\x00g\x00e\x00i\x00c\x00o\x00n\x00s\x00C\x00i\x00r\x00c\x00l\x00e\x00A\x00r\
\x00r\x00o\x00w\x00D\x00o\x00w\x00n\x000\x002\x00.\x00s\x00v\x00g\
\x00\x0e\
\x06\x01\x0a\xc7\
\x00C\
\x00o\x00m\x00p\x00a\x00n\x03\x03\x00i\x03\x01\x00a\x00.\x00s\x00v\x00g\
\x00\x16\
\x03\x8c\x22'\
\x00I\
\x00c\x00B\x00a\x00s\x00e\x00l\x00i\x00n\x00e\x00S\x00e\x00t\x00t\x00i\x00n\x00g\
\x00s\x00.\x00s\x00v\x00g\
\x00\x09\
\x03\xa4\xcfG\
\x00D\
\x00e\x00l\x00t\x00a\x00.\x00s\x00v\x00g\
\x00\x09\
\x09\xc2\xf7\xc7\
\x00P\
\x00a\x00s\x00e\x00o\x00.\x00s\x00v\x00g\
\x00\x16\
\x0e\xa14\x07\
\x00I\
\x00c\x00o\x00n\x00o\x00i\x00r\x00X\x00m\x00a\x00r\x00k\x00C\x00i\x00r\x00c\x00l\
\x00e\x00.\x00s\x00v\x00g\
"

qt_resource_struct = b"\
\x00\x00\x00\x00\x00\x02\x00\x00\x00\x01\x00\x00\x00\x01\
\x00\x00\x00\x00\x00\x00\x00\x00\
\x00\x00\x00\x00\x00\x02\x00\x00\x00\x01\x00\x00\x00\x02\
\x00\x00\x00\x00\x00\x00\x00\x00\
\x00\x00\x00\x12\x00\x02\x00\x00\x00 \x00\x00\x00\x03\
\x00\x00\x00\x00\x00\x00\x00\x00\
\x00\x00\x00.\x00\x00\x00\x00\x00\x01\x00\x00\x00\x00\
\x00\x00\x01\x95^\x86_\xec\
\x00\x00\x05Z\x00\x00\x00\x00\x00\x01\x00\x00\xf1\x15\
\x00\x00\x01\x95^\x86B\x1e\
\x00\x00\x05\x8c\x00\x00\x00\x00\x00\x01\x00\x00\xf44\
\x00\x00\x01\x97\x15\x1aI\xed\
\x00\x00\x01\x94\x00\x00\x00\x00\x00\x01\x00\x00\x0bl\
\x00\x00\x01\x97\x14\x19\x13E\
\x00\x00\x03 \x00\x00\x00\x00\x00\x01\x00\x00p\xd3\
\x00\x00\x01\x97\x14\x199p\
\x00\x00\x02P\x00\x00\x00\x00\x00\x01\x00\x00g\x98\
\x00\x00\x01\x95^|\xe1\xd5\
\x00\x00\x01\xe0\x00\x00\x00\x00\x00\x01\x00\x00P\x0d\
\x00\x00\x01\x95^}\xd5\xd8\
\x00\x00\x02\xa6\x00\x00\x00\x00\x00\x01\x00\x00k\xc3\
\x00\x00\x01\x95\xacT\xb6\xc4\
\x00\x00\x04\xd2\x00\x00\x00\x00\x00\x01\x00\x00\xcc\xe8\
\x00\x00\x01\x95^z\xb2\xc7\
\x00\x00\x00h\x00\x00\x00\x00\x00\x01\x00\x00\x01\xb2\
\x00\x00\x01\x95^z\xcd\xb4\
\x00\x00\x03\xfe\x00\x00\x00\x00\x00\x01\x00\x00\xb1\x1c\
\x00\x00\x01\x96\xd5\x93\x88a\
\x00\x00\x058\x00\x00\x00\x00\x00\x01\x00\x00\xcfx\
\x00\x00\x01\x97\x14\x19-\x85\
\x00\x00\x02,\x00\x00\x00\x00\x00\x01\x00\x00f-\
\x00\x00\x01\x95^z\x94\xde\
\x00\x00\x00\x90\x00\x00\x00\x00\x00\x01\x00\x00\x02\xa7\
\x00\x00\x01\x95\xac>\xd5\x81\
\x00\x00\x03\xc4\x00\x00\x00\x00\x00\x01\x00\x00\x92\xfc\
\x00\x00\x01\x95^z\xf1\xc5\
\x00\x00\x02r\x00\x00\x00\x00\x00\x01\x00\x00i=\
\x00\x00\x01\x95^\x9a\x04\xd4\
\x00\x00\x05\xa4\x00\x01\x00\x00\x00\x01\x00\x00\xf7\x92\
\x00\x00\x01\x97\x14\x196\xb0\
\x00\x00\x01\x12\x00\x00\x00\x00\x00\x01\x00\x00\x06O\
\x00\x00\x01\x95\xacQbv\
\x00\x00\x03f\x00\x00\x00\x00\x00\x01\x00\x00\x90\xf8\
\x00\x00\x01\x95^zW]\
\x00\x00\x04\x98\x00\x00\x00\x00\x00\x01\x00\x00\xc3E\
\x00\x00\x01\x95^|\x9b\xcd\
\x00\x00\x01T\x00\x00\x00\x00\x00\x01\x00\x00\x08\x88\
\x00\x00\x01\x95\xacSv4\
\x00\x00\x02\xdc\x00\x00\x00\x00\x00\x01\x00\x00oZ\
\x00\x00\x01\x95\xac>\xa6<\
\x00\x00\x04l\x00\x01\x00\x00\x00\x01\x00\x00\xbb\x04\
\x00\x00\x01\x97\x14\x190\xdf\
\x00\x00\x04<\x00\x00\x00\x00\x00\x01\x00\x00\xb2\x99\
\x00\x00\x01\x95^}Wd\
\x00\x00\x03\x9c\x00\x00\x00\x00\x00\x01\x00\x00\x91\xde\
\x00\x00\x01\x95^z4\x09\
\x00\x00\x05\xbc\x00\x00\x00\x00\x00\x01\x00\x00\xfe'\
\x00\x00\x01\x95^y\xd0(\
\x00\x00\x02\x14\x00\x00\x00\x00\x00\x01\x00\x00Q\x1b\
\x00\x00\x01\x97\x14\x193\xd6\
\x00\x00\x03\xe8\x00\x00\x00\x00\x00\x01\x00\x00\x93\xdb\
\x00\x00\x01\x97\x14\x19'\x04\
\x00\x00\x00\xd2\x00\x00\x00\x00\x00\x01\x00\x00\x04\x1f\
\x00\x00\x01\x97A6*i\
\x00\x00\x04\xf6\x00\x00\x00\x00\x00\x01\x00\x00\xcd\xf9\
\x00\x00\x01\x95\xac>qy\
\x00\x00\x01\xc6\x00\x00\x00\x00\x00\x01\x00\x00'\x00\
\x00\x00\x01\x97\x14\x19*e\
\x00\x00\x03:\x00\x00\x00\x00\x00\x01\x00\x00\x8f\xd5\
\x00\x00\x01\x95^{.\x07\
"

def qInitResources():
    QtCore.qRegisterResourceData(0x03, qt_resource_struct, qt_resource_name, qt_resource_data)

def qCleanupResources():
    QtCore.qUnregisterResourceData(0x03, qt_resource_struct, qt_resource_name, qt_resource_data)

qInitResources()
